nevermore3d/StealthMax/UserMods/Lid Front Hinge - Annex (by LarZem)/README.md

A Lid Front Hinge with custom engraving.
