nevermore3d/StealthMax/UserMods/Nevermore StealthMax PCB (by Isik's Tech)/README.md

[Nevermore StealthMax PCB (GitHub Repository)](https://github.com/xbst/Nevermore-PCB)
