nevermore3d/StealthMax/UserMods/Top Panel Mount (by 0ndsk4)/README.md

An early prototype top panel mount for the StealthMax which has since been discontinued in favor of the Direct On Panel Mount. 
Requires a Voron cutout in the top panel.
