nevermore3d/StealthMax/assets/_unsorted/PCO/README.md

# **Photocatalytic Addon**

Note: As of yet unknown efficiency - print for feedback or improvements (within Creative Commons Attribution) to make this addon as awesome as possible!

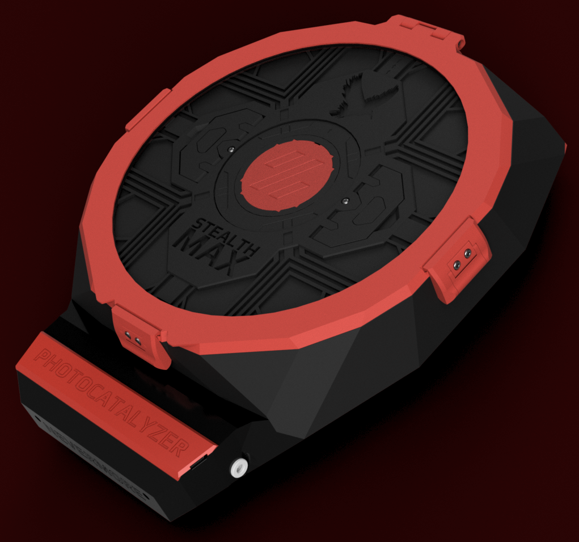
[picture p13: assets/renders/pco2.png]


# **PCO Filtration Addon: A Sun-Inspired Solution for Cleaner Air**

PCO Filtration ingeniously mirrors what the sun accomplishes with VOCs (Volatile Organic Compounds) in our atmosphere. Under natural conditions, UV rays from the sun interact with VOCs and, with the help of other elements in the air, break them down into "harmless" CO<sub>2</sub>. What if we could harness this process in our filtration systems?

**UVC** lights, set at a non-ozone-producing safe wavelength of 275nm, energize a **TiO<sub>2</sub>** (titanium dioxide) mesh, triggering electron conformation changes. Water molecules passing by react with the energized mesh, producing **hydroxyl radicals** and other reactive species that **"attack" VOCs**, effectively chopping them into smaller pieces. 

While simple VOCs can be broken down to the smallest unit of CO<sub>2</sub> rapidly, larger and more complex VOCs might necessitate multiple passes and hydroxyl radical "chops". Over time, the photocatalytic filter addon progressively degrades the contaminants. 

# Utility Across Various Fronts:
**Enhanced Efficiency:** 

VOCs that resist carbon capture may transform into a different type of VOC that is more readily trapped by filtration media, thereby enhancing the combined efficiency. Although photocatalytic filtration is generally slower than swift HEPA or carbon capture, it plays a crucial role.

**Persistent Cleanliness**: 

The PCO addon can operate even between prints to counteract styrene residue from surface off-gassing, or even from the carbon filtration media itself as the carbon ages, ensuring cleaner air for extended periods.

**Adaptability to Heat**: 

As the chamber’s temperature rises, the efficiency of carbon diminishes. Approximately at 60°C, carbon filtration becomes suboptimal. Conversely, photocatalytic reactivity benefits from the heat energy in the air, positioning the PCO addon as an excellent strategy to conserve carbon by allowing it to cool off while utilizing the heat to eliminate VOCs photocatalytically!

# BOM and Materials for an Alpha unit

Note: These are affiliate links. Please use them to support the project at no additional cost. Or don't - that's up to you!
| | Amount | Part | Source |
| ---- | ----: | ---- | :----: |
| **Electronics** |  2 pc | 14520 275nnm UVC (2.5W _or_ 6W) <sup>1</sup> | [AliExpress](https://s.click.aliexpress.com/e/_DDsC6F1) <BR>[AliExpress](https://s.click.aliexpress.com/e/_DDy4ivB)<BR>[AliExpress](https://www.aliexpress.com/item/4000898731245.html) |
| |  1 pcs | TiO<sub>2</sub> Photocatalysis Mesh <sup>2</sup> | [AliExpress](https://s.click.aliexpress.com/e/_DC8levV) |
| |  1 pcs | HEPA filter (for Xiaomi Mijia G1) | [AliExpress](https://s.click.aliexpress.com/e/_EGPsFBt) |
| |  2 pc | 3010 Blower Fans | [AliExpress](https://s.click.aliexpress.com/e/_DCLQtaj) |
| |  1 pc | 12V Single Channel Relay | [AliExpress](https://s.click.aliexpress.com/e/_Dmt3tRH) |
| **Fasteners** |  1 pcs | M8 threaded DC connector | [AliExpress](https://www.aliexpress.com/item/33001103693.html?spm=a2g0o.order_list.order_list_main.89.50ea1802RQAeZj) |
| | 8 pcs | M3x6 BHCS <sup>3</sup> | [AliExpress](https://s.click.aliexpress.com/e/_DduS2Vn) |
| | 6 pcs | M3x10 SHCS | [AliExpress](https://s.click.aliexpress.com/e/_DkxhzGZ) |
| |  4 pc | M3 Hex Nut | |
| |  2 pc | M3xD5.0xL4.0 Heat Set Inserts  | [AliExpress](https://s.click.aliexpress.com/e/_DeVF8rT) | |  

*<sup>1</sup>*  2.5W likely enough, but a stronger light will make a stronger reaction and give margin for UV degradation (80% strength left after 1000hrs seems pretty standard), but its unknown if the added heat creates a problem.<br>
*<sup>2</sup>*  3mm mesh cut with scissors to two pieces of approximately 128x40mm. A single 500x500mm sheet will thus be enough for _alot_ of TiO<sub>2</sub> filters<br>
*<sup>3</sup>*  Two of these slots are made for SHCS bolts if you've got them, but BHCS will fit just as well<br>

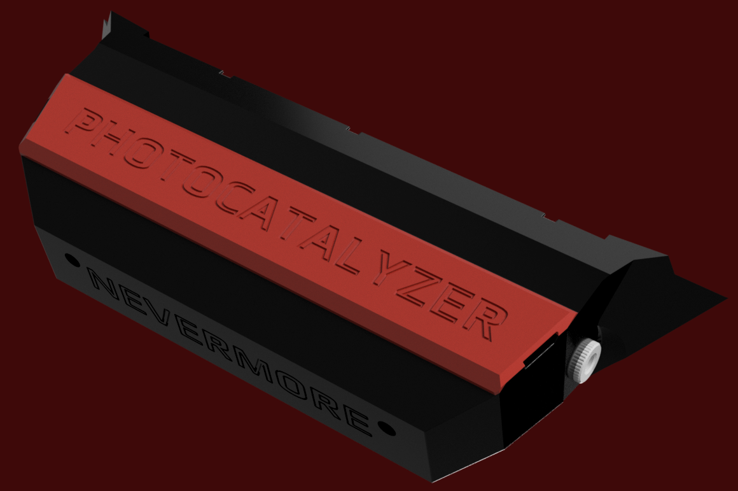
[picture p14: assets/renders/pco1.png]
