nevermore3d/StealthMax/assets/_unsorted/Stealthmax_S/README.md

StealthMax
# **Stealthmax [S]**
Lets decrease size a bit shall we, in order to print the Stealthmax on machines with a 250mm bed? 

**StealthMax [S]** is what we end up with - reworked from the ground up, its both 20% [**S**]maller than a regular Stealthmax, as well as much more [**S**]ilent due to the smaller, lower noise fan. See BOM below (purchase links linked on the main page).

- The 65mm GPU Fan has been swapped for a [**60mm Delta KFB0612HAFDB**](https://www.onetwo3d.co.uk/product/delta-kfb0612hafdb-fan/?wpam_id=2) It has less air flow at 9.15cfm unrestricted, but on the other hand is much less noisy. The unrestrictive nature of a stealthmax circular basket also allows for much more usable airflow from this fan compared to a smaller filter design. 
- The panel has shrunken to **200mm @ 3mm** thickness.
- Mounting points for VOC sensors has changed compared to the regular stealthmax.
- **Hepa filters** have been changed to new [**Nevermore Mini HEPA**](https://www.onetwo3d.co.uk/product/hepa-filter-for-nevermore-mini/?wpam_id=2), which means the total carbon depth (equaling efficiency) of the filter has not decreased more than a bit over one centimeter compared to the original Stealthmax.
- Quick and easy sourcing? Check out the electronics/fasteners/hepa/carbon [**Stealthmax S Filter Kit**](https://www.onetwo3d.co.uk/product/nevermore-stealthmax-s-filter-kit-advanced/?wpam_id=2) from OT3D!
- Most everything else remains the same from the regular BOM, including sensors, pico, buck converter, with just a few minor bolt changes: see out interactive [BOM / Sourcing Guide](https://bit.ly/NeveremoreStealthMaxBOM)

Heres how the smaller version compares to the larger:
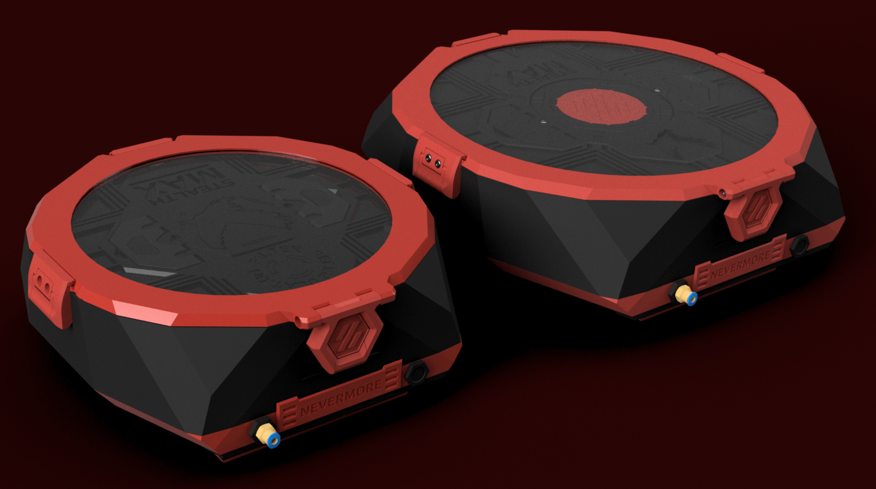
[picture p15: assets/renders/sm_250_300_comparison.png]

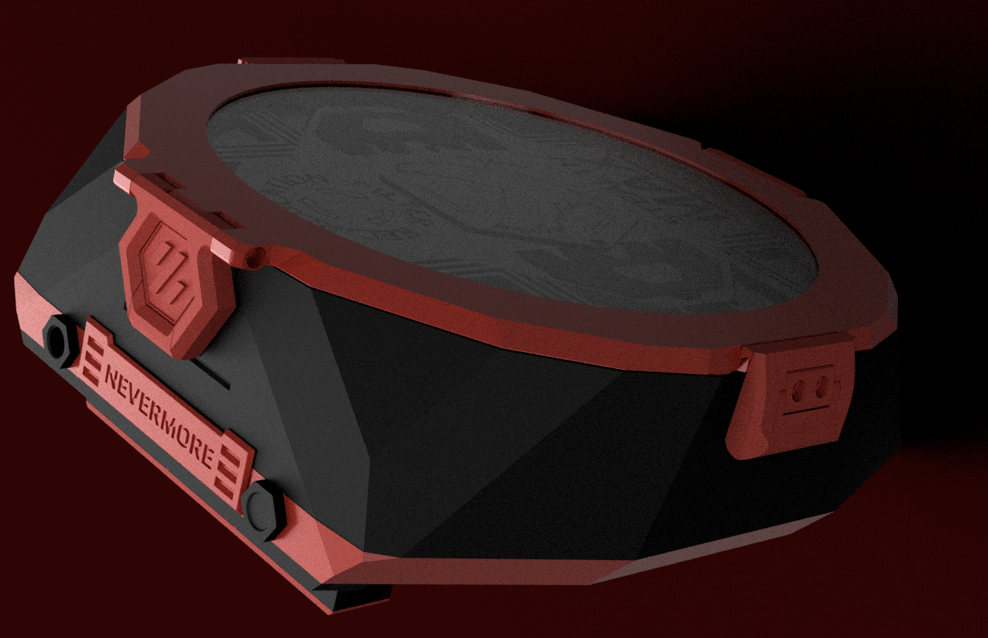
[picture p16: assets/renders/sm_250.png]
