nevermore3d/StealthMax/STLs/4_AddOns/4.1_PCOFiltration/readme.md

NOTE: The PCO Addon will be replaced with a PCO Hub module - more efficient than the original prototype - in the coming year. Stay tuned.
