nevermore3d/StealthMax/STLs/3_Lid/3.3_LidLatch.stl

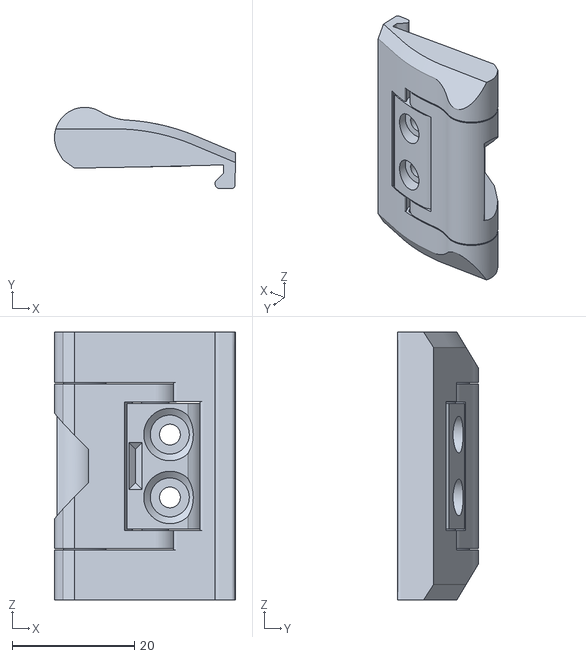
[picture p92: CAD file, 2024-05-04]
STLs/3_Lid/3.3_LidLatch.stl
29.6 x 13.3 x 43.9
