nevermore3d/StealthMax/STLs/3_Lid/StealthMax/M_3.0_LidFrame.stl

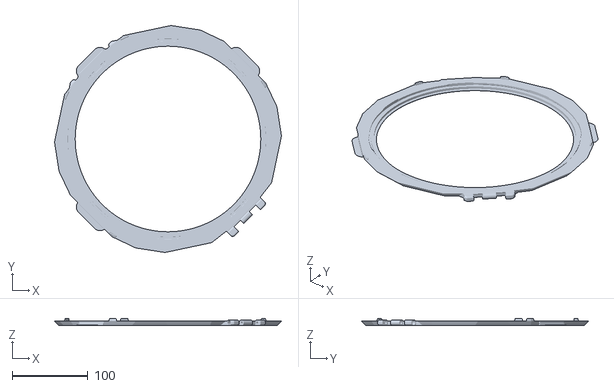
[picture p93: CAD file, 2024-05-31]
STLs/3_Lid/StealthMax/M_3.0_LidFrame.stl
300.3 x 300.3 x 9.00
