nevermore3d/StealthMax/STLs/3_Lid/StealthMax_S/S_3.0_LidFrame.stl

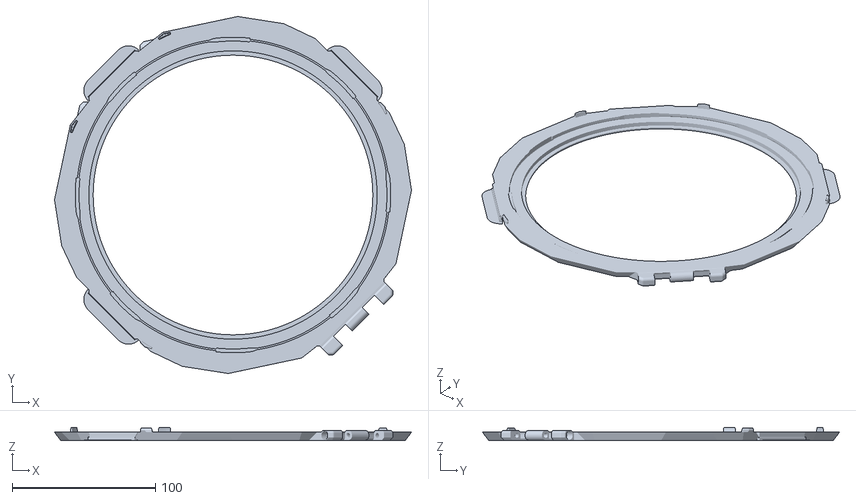
[picture p94: CAD file, 2024-05-31]
STLs/3_Lid/StealthMax_S/S_3.0_LidFrame.stl
249.3 x 249.3 x 9.00
