nevermore3d/StealthMax/STLs/4_AddOns/4.0_CPAPTubeIntake/4.0.0_IntakeAdapterLeft.stl

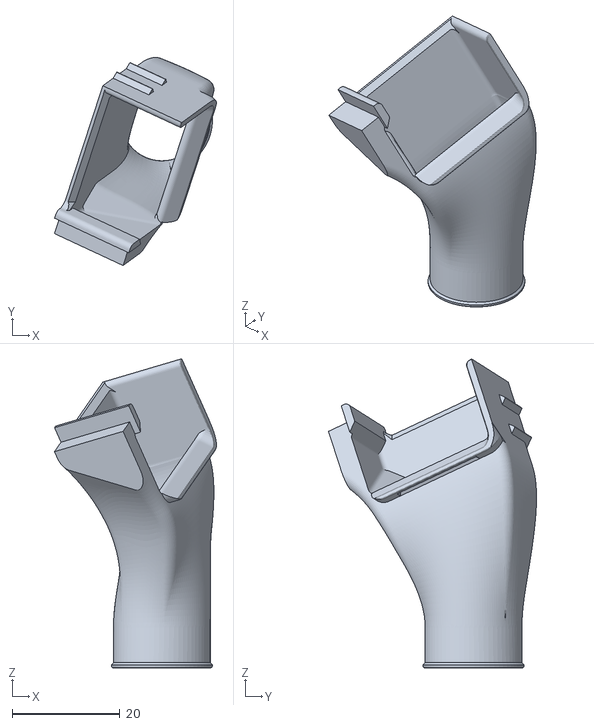
[picture p95: CAD file, 2024-08-18]
STLs/4_AddOns/4.0_CPAPTubeIntake/4.0.0_IntakeAdapterLeft.stl
30.1 x 38.7 x 57.4
