nevermore3d/StealthMax/UserMods/[Parametric] Exhaust Pipe (by FatalBulletHit)/STLs/ExhaustPipe_DOPM_4mm.stl

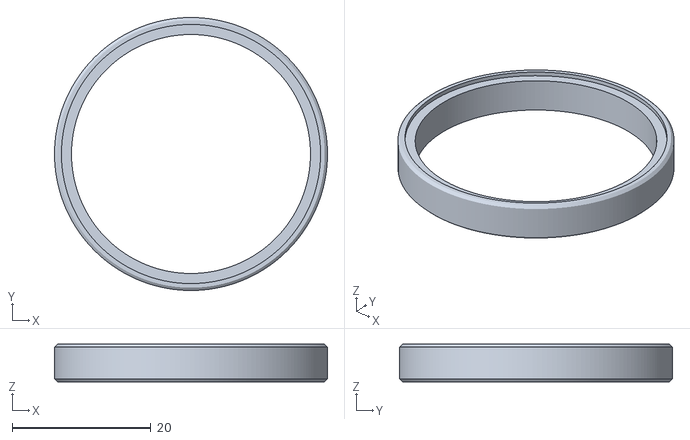
[picture p96: CAD file, 2024-03-18]
UserMods/[Parametric] Exhaust Pipe (by FatalBulletHit)/STLs/ExhaustPipe_DOPM_4mm.stl
39.3 x 39.3 x 5.40
