nevermore3d/StealthMax/UserMods/[Parametric] Lid Frame (by 0ndsk4)/4mm/S_LidPanelHolder_4mm.stl

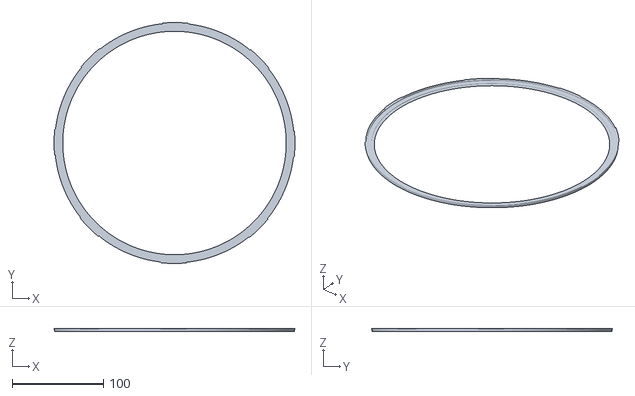
[picture p97: CAD file, 2023-06-20]
UserMods/[Parametric] Lid Frame (by 0ndsk4)/4mm/S_LidPanelHolder_4mm.stl
264.8 x 264.8 x 3.40
