nevermore3d/StealthMax/UserMods/[Parametric] Lid Frame (by 0ndsk4)/One_Eighth_in_10inch/S_LidPanelHolder_One_Eighth_in_10inch.stl

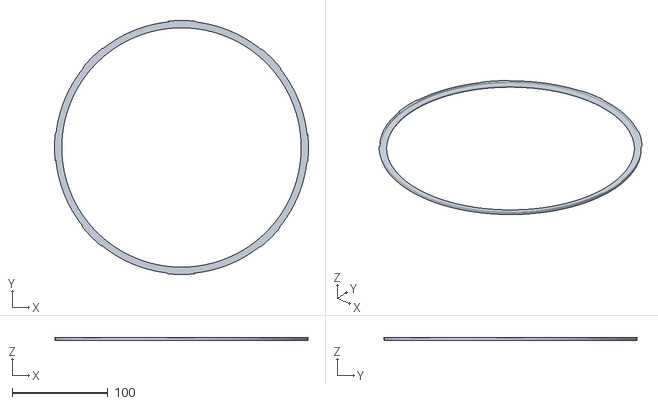
[picture p98: CAD file, 2023-06-20]
UserMods/[Parametric] Lid Frame (by 0ndsk4)/One_Eighth_in_10inch/S_LidPanelHolder_One_Eighth_in_10inch.stl
264.8 x 264.8 x 3.40
