nevermore3d/StealthMax/UserMods/Bowden Cap - ECAS (by Blamm)/BowdenCap_ECAS.stl

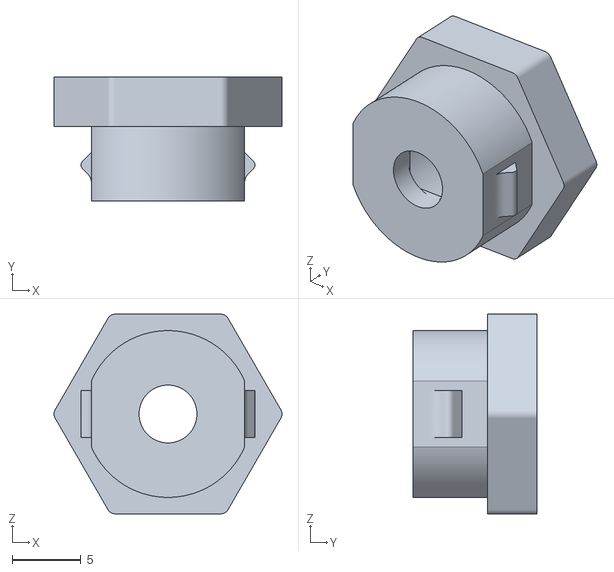
[picture p100: CAD file, 2024-10-31]
UserMods/Bowden Cap - ECAS (by Blamm)/BowdenCap_ECAS.stl
16.5 x 9.00 x 14.5
