nevermore3d/StealthMax/UserMods/Bowden Cap - PG7 (by FatalBulletHit)/Bowden Cap PG7 (by FatalBulletHit).step

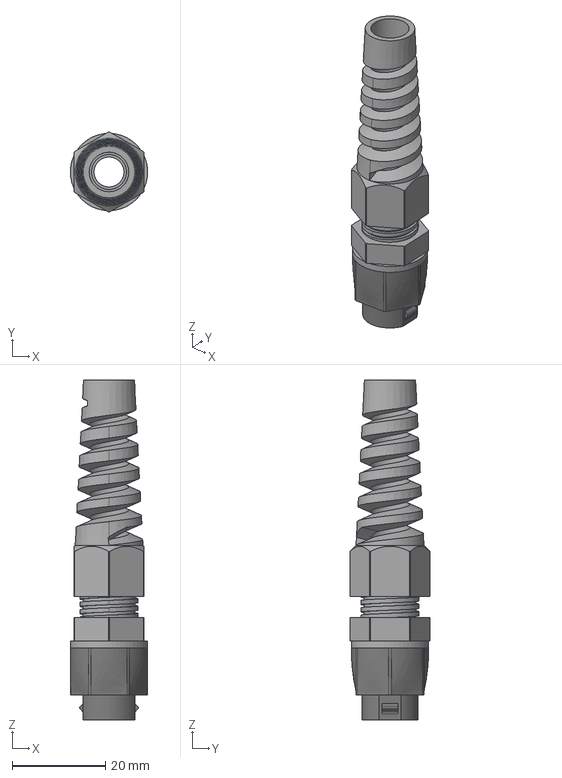
[picture p101: CAD file, 2024-05-31]
UserMods/Bowden Cap - PG7 (by FatalBulletHit)/Bowden Cap PG7 (by FatalBulletHit).step
16.6 x 17.2 x 73.0 mm
1.3b_BowdenCap_Open
bsspx-21-w_1
