nevermore3d/StealthMax/UserMods/Cable Entry Cap - Micro-Fit 5 Pin (by everydaybludger)/CableEntryCap_MicroFit5.stl

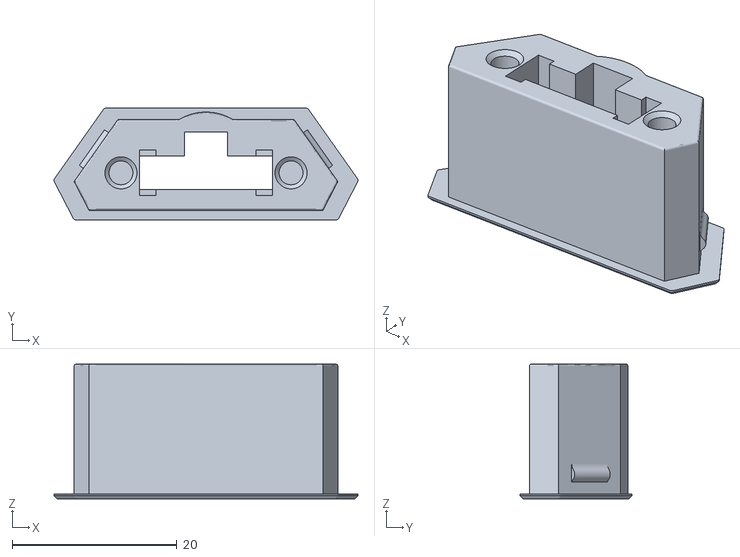
[picture p102: CAD file, 2024-03-18]
UserMods/Cable Entry Cap - Micro-Fit 5 Pin (by everydaybludger)/CableEntryCap_MicroFit5.stl
36.9 x 13.6 x 16.4
