nevermore3d/StealthMax/UserMods/Cable Entry Cap - Open Inlet (by AdamV3D)/Cable Entry Cap - Open Inlet (by AdamV3D).step

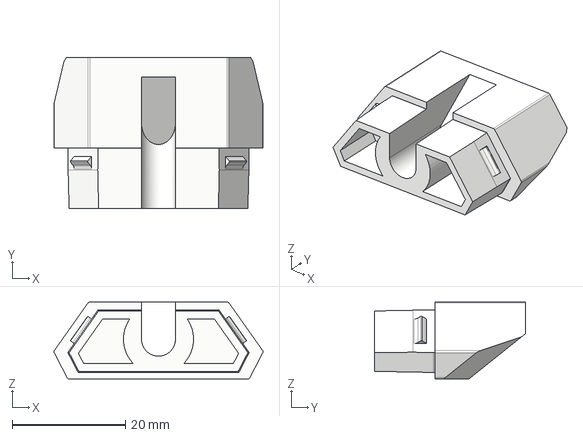
[picture p103: CAD file, 2024-05-31]
UserMods/Cable Entry Cap - Open Inlet (by AdamV3D)/Cable Entry Cap - Open Inlet (by AdamV3D).step
36.9 x 26.7 x 13.6 mm
