nevermore3d/StealthMax/UserMods/Cable Entry Cap - QtPy (by fboc)/CableEntryCap_QtPy.stl

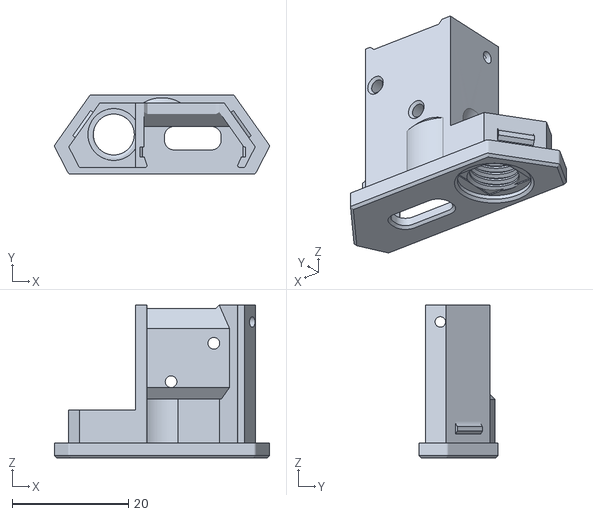
[picture p104: CAD file, 2023-12-06]
UserMods/Cable Entry Cap - QtPy (by fboc)/CableEntryCap_QtPy.stl
36.9 x 13.6 x 26.3
