nevermore3d/StealthMax/UserMods/Cable Entry Cap - USB (by Tuba)/CableEntryCap_USB.stl

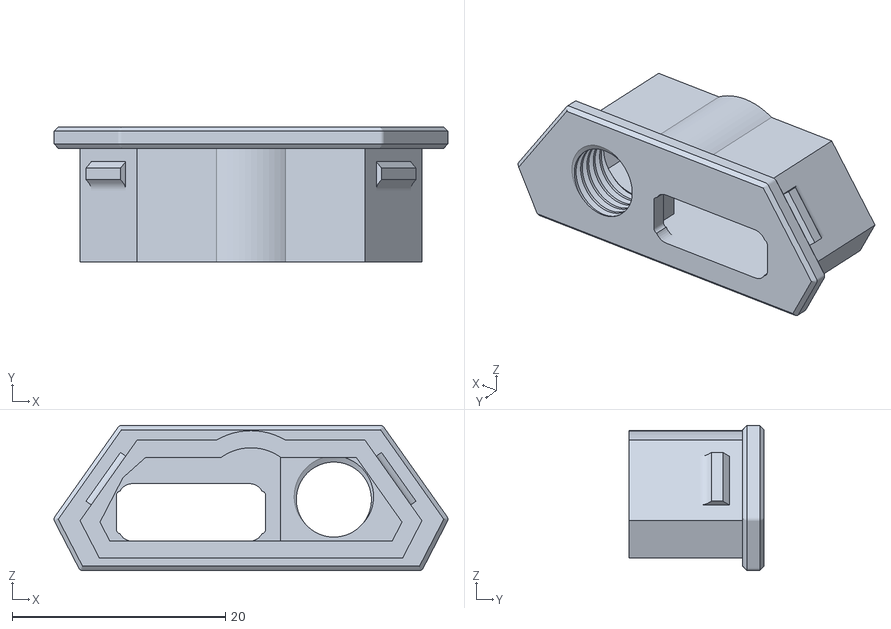
[picture p105: CAD file, 2023-10-12]
UserMods/Cable Entry Cap - USB (by Tuba)/CableEntryCap_USB.stl
36.9 x 12.7 x 13.6
