nevermore3d/StealthMax/UserMods/Chamber Exhaust Connection - Upwards Flow (by AdamV3D)/Chamber Exhaust Connection - Upwards Flow (by AdamV3D).step

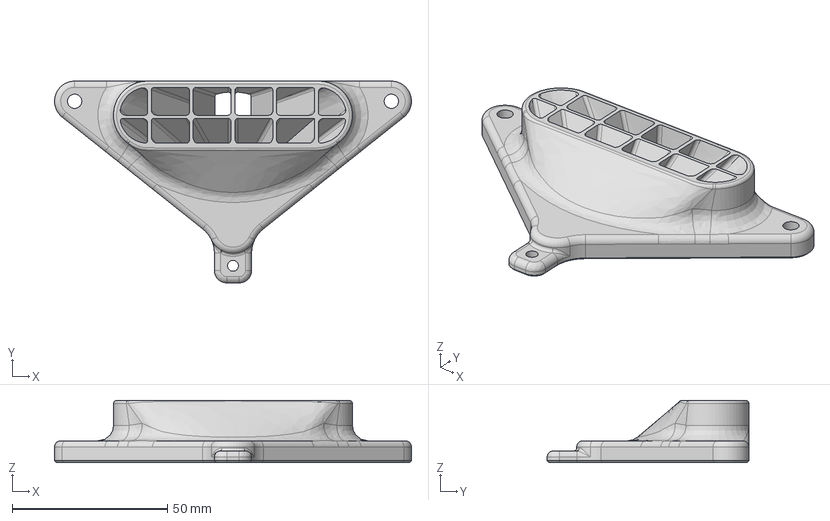
[picture p106: CAD file, 2024-05-31]
UserMods/Chamber Exhaust Connection - Upwards Flow (by AdamV3D)/Chamber Exhaust Connection - Upwards Flow (by AdamV3D).step
115.0 x 65.0 x 20.0 mm
