nevermore3d/StealthMax/UserMods/ERCF Mount (by BO_Andy)/ERCFMount.stl

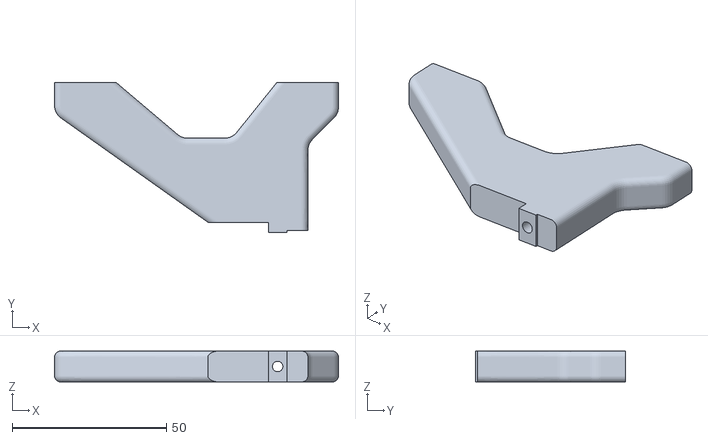
[picture p107: CAD file, 2023-12-10]
UserMods/ERCF Mount (by BO_Andy)/ERCFMount.stl
92.0 x 48.6 x 10.0
