nevermore3d/StealthMax/UserMods/Fan Wire Pin (Extra Long) (by SirRenix)/FanWirePin_ExtraLong.stl

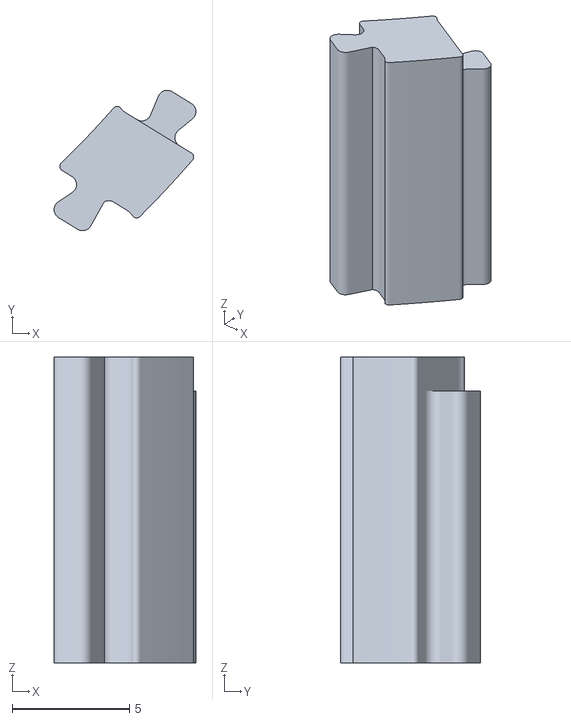
[picture p108: CAD file, 2024-03-13]
UserMods/Fan Wire Pin (Extra Long) (by SirRenix)/FanWirePin_ExtraLong.stl
6.05 x 5.99 x 13.1
