nevermore3d/StealthMax/UserMods/Flow Chamber Fan Hole Plug (by SirRenix)/FlowChamberFanHolePlug.stl

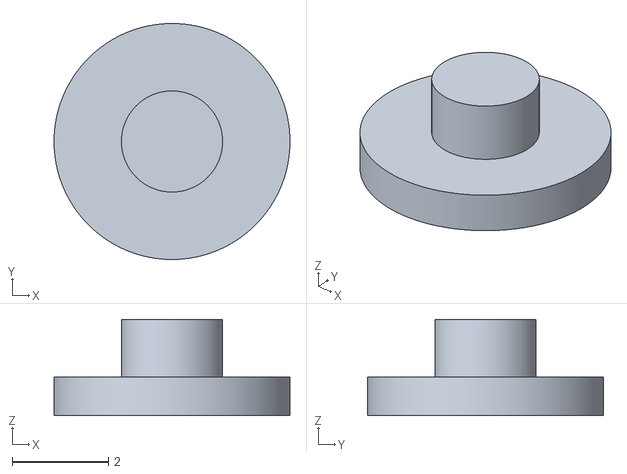
[picture p109: CAD file, 2024-03-18]
UserMods/Flow Chamber Fan Hole Plug (by SirRenix)/FlowChamberFanHolePlug.stl
4.90 x 4.90 x 2.00
