nevermore3d/StealthMax/UserMods/Ghetto Panel (by TessaKavanagh)/M_GhettoPanel.stl

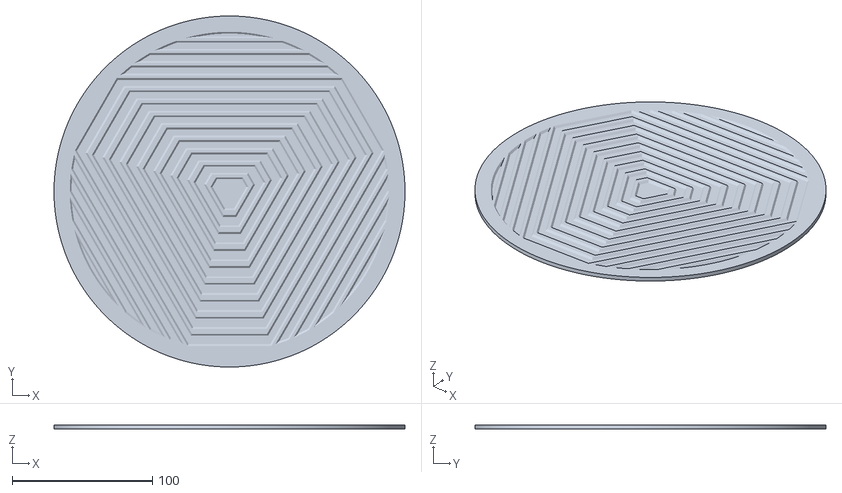
[picture p110: CAD file, 2024-03-13]
UserMods/Ghetto Panel (by TessaKavanagh)/M_GhettoPanel.stl
250.0 x 250.0 x 3.00
