nevermore3d/StealthMax/UserMods/Lid Frame - Extra Clearance (by AdamV3D)/Lid Frame - Extra Clearance (by AdamV3D).step

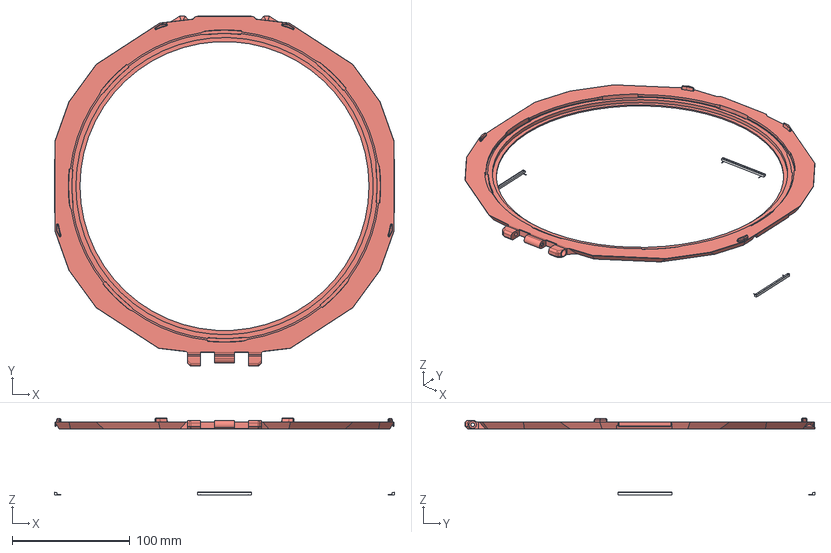
[picture p111: CAD file, 2024-05-31]
UserMods/Lid Frame - Extra Clearance (by AdamV3D)/Lid Frame - Extra Clearance (by AdamV3D).step
288.8 x 297.2 x 65.0 mm
