nevermore3d/StealthMax/UserMods/Lid Front Hinge - 2 Part Version (by AdamV3D)/Lid Front Hinge - 2 Part Version (by AdamV3D).step

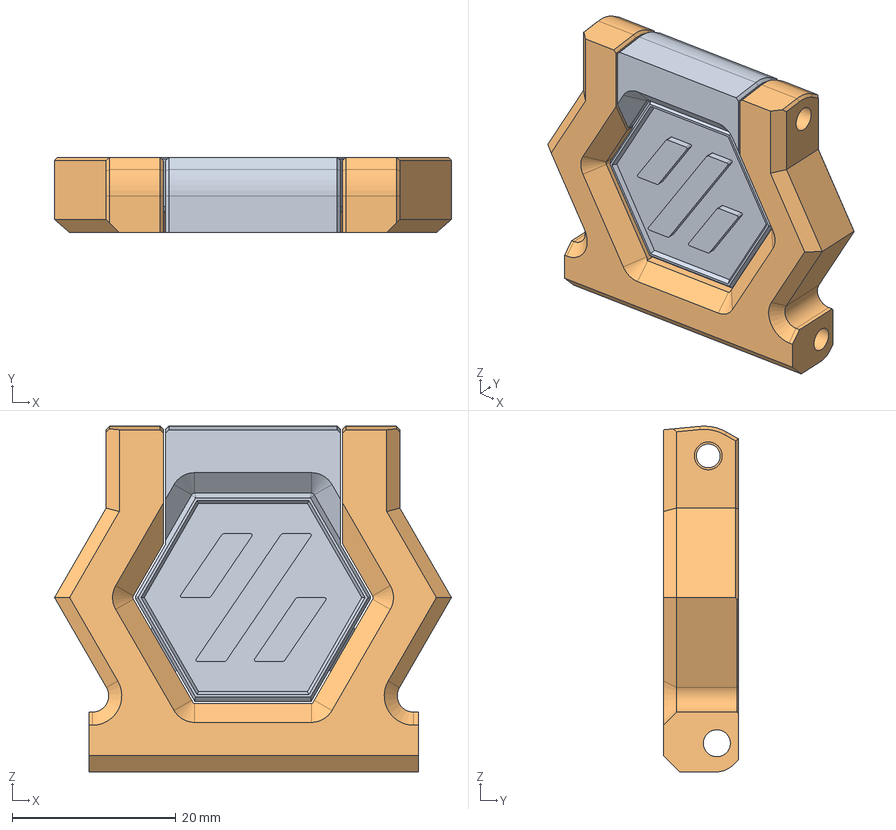
[picture p112: CAD file, 2024-05-31]
UserMods/Lid Front Hinge - 2 Part Version (by AdamV3D)/Lid Front Hinge - 2 Part Version (by AdamV3D).step
48.5 x 9.18 x 42.2 mm
