nevermore3d/StealthMax/UserMods/Lid Front Hinge - Annex (by LarZem)/LidFrontHinge_Annex.stl

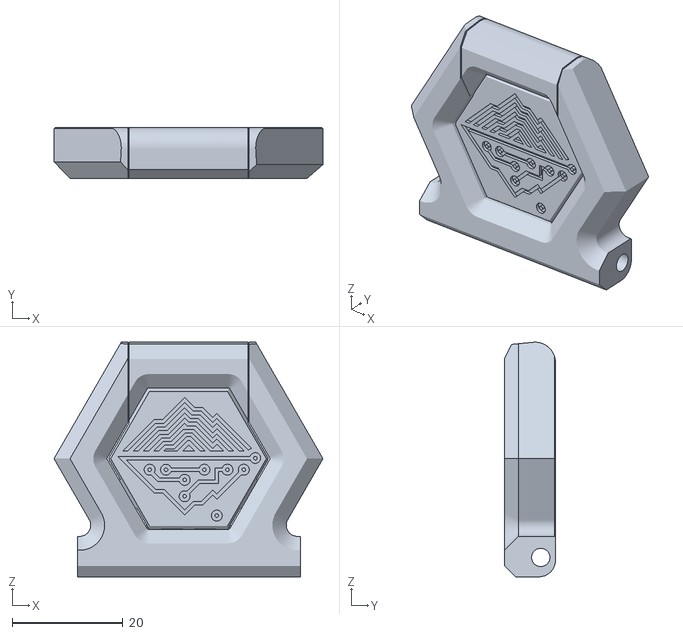
[picture p113: CAD file, 2023-12-06]
UserMods/Lid Front Hinge - Annex (by LarZem)/LidFrontHinge_Annex.stl
48.5 x 9.18 x 42.3
