nevermore3d/StealthMax/UserMods/Lid Panel Holder - Easy Turn (by AdamV3D)/Lid Panel Holder - Easy Turn (by AdamV3D).step

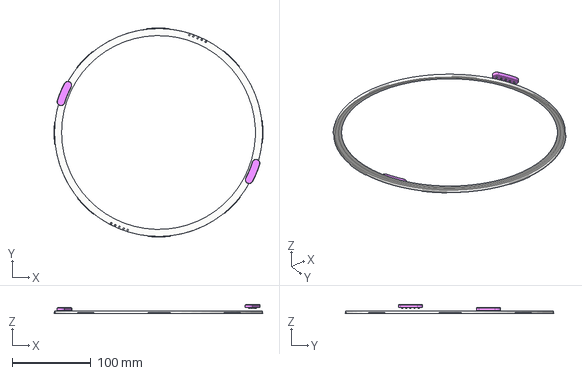
[picture p114: CAD file, 2024-05-31]
UserMods/Lid Panel Holder - Easy Turn (by AdamV3D)/Lid Panel Holder - Easy Turn (by AdamV3D).step
264.7 x 264.7 x 11.4 mm
Gripper x 2
