nevermore3d/StealthMax/UserMods/Sensor Holder - Mag Carrier (by 0ndsk4)/Sensor Holder Mag Carrier (by 0ndsk4).step

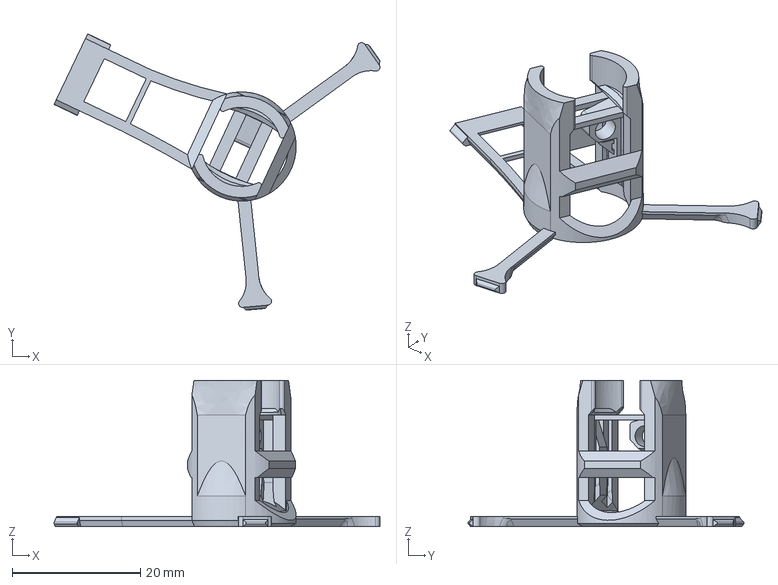
[picture p115: CAD file, 2024-03-18]
UserMods/Sensor Holder - Mag Carrier (by 0ndsk4)/Sensor Holder Mag Carrier (by 0ndsk4).step
50.8 x 43.0 x 22.8 mm
