nevermore3d/StealthMax/UserMods/Toggleable Channel DOPM FlowChamber (by VIN-y)/10_NM_StealthMax_Mod_v3-Output_Funnel.stl

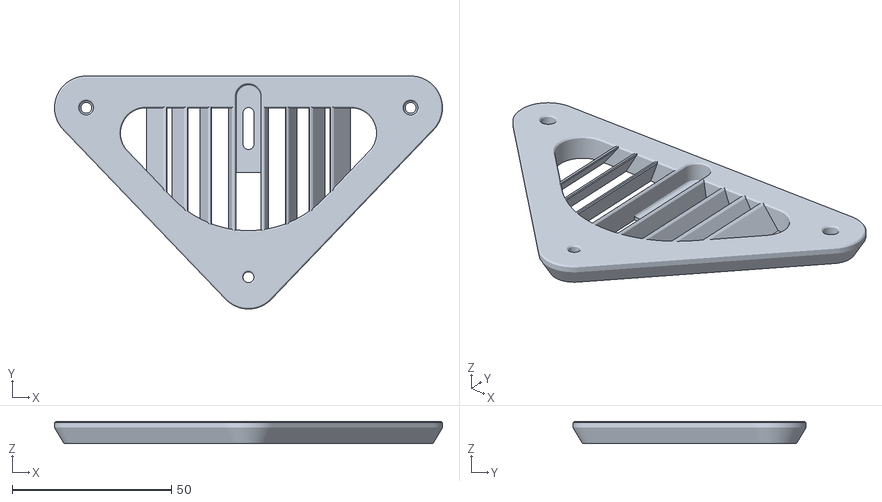
[picture p116: CAD file, 2024-10-18]
UserMods/Toggleable Channel DOPM FlowChamber (by VIN-y)/10_NM_StealthMax_Mod_v3-Output_Funnel.stl
121.9 x 73.2 x 7.00
