nevermore3d/StealthMax/UserMods/Toggleable Channel DOPM FlowChamber (by VIN-y)/CADs/10_NM_StealthMax_Mod-Switch.step

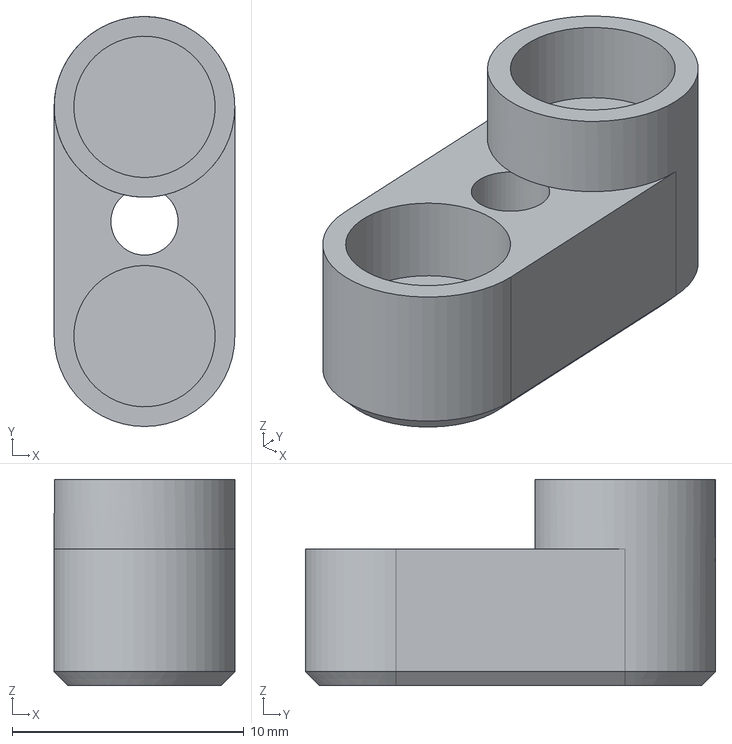
[picture p117: CAD file, 2024-10-18]
UserMods/Toggleable Channel DOPM FlowChamber (by VIN-y)/CADs/10_NM_StealthMax_Mod-Switch.step
7.80 x 17.7 x 8.90 mm
