nevermore3d/StealthMax/UserMods/Top Panel Mount (by 0ndsk4)/Top Panel Mount (by 0ndsk4).step

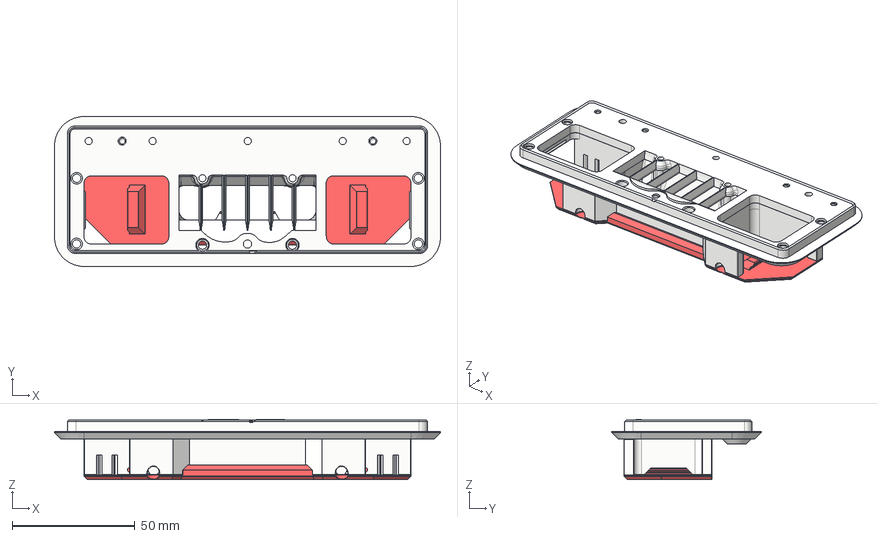
[picture p118: CAD file, 2024-03-13]
UserMods/Top Panel Mount (by 0ndsk4)/Top Panel Mount (by 0ndsk4).step
157.0 x 61.0 x 24.6 mm
Chamber Side (1)
Voron Exhaust Fitting (1)
