nevermore3d/StealthMax/UserMods/Umbilical entry via flow chamber (by igiannakas)/StealthMax 300 flow chamber for umbilical.stl

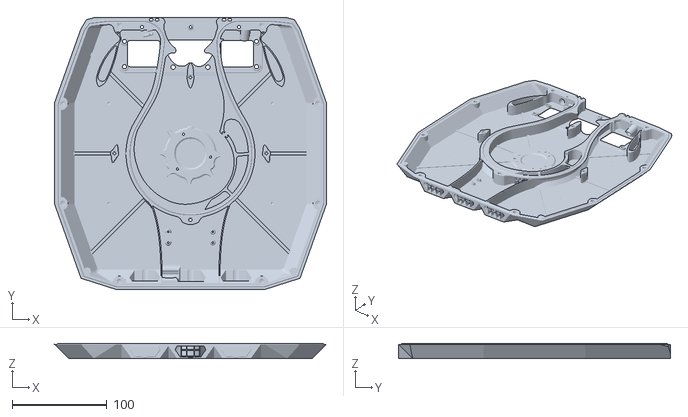
[picture p119: CAD file, 2024-05-31]
UserMods/Umbilical entry via flow chamber (by igiannakas)/StealthMax 300 flow chamber for umbilical.stl
286.4 x 286.4 x 15.9
