nevermore3d/StealthMax/UserMods/Umbilical Mount BPM (by fronti)/umbilical-mount-bpm.stl

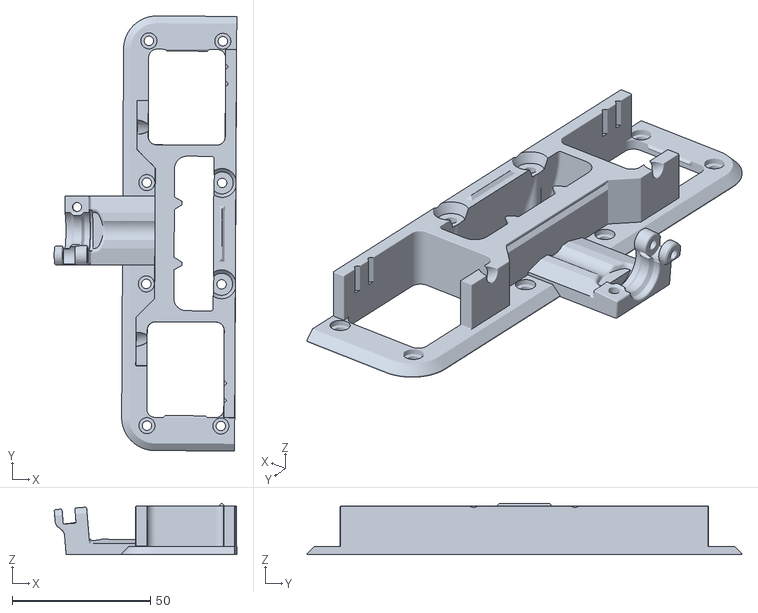
[picture p120: CAD file, 2024-12-13]
UserMods/Umbilical Mount BPM (by fronti)/umbilical-mount-bpm.stl
66.0 x 157.1 x 18.5
