nevermore3d/StealthMax/UserMods/Voron Exhaust Fitting - ERCF Filament Motion Sensor (by ManuC)/StealthMax_-_FilamentSensor-_Left.stl

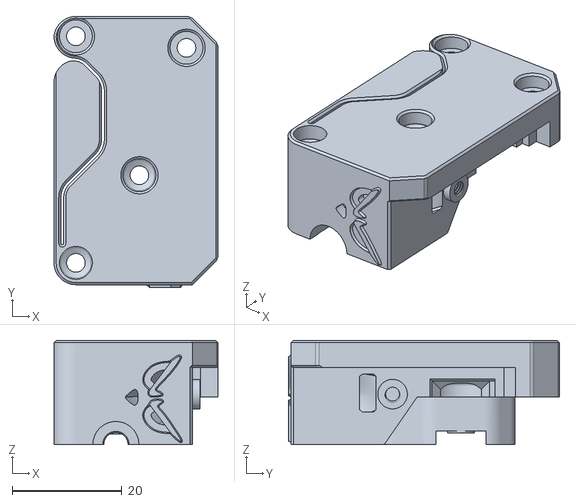
[picture p121: CAD file, 2024-03-18]
UserMods/Voron Exhaust Fitting - ERCF Filament Motion Sensor (by ManuC)/StealthMax_-_FilamentSensor-_Left.stl
29.9 x 49.5 x 19.0
