nevermore3d/StealthMax/UserMods/Voronexhaustfitting_BPM- BTT smart filament sensor/bowdencap_ptfe.stl

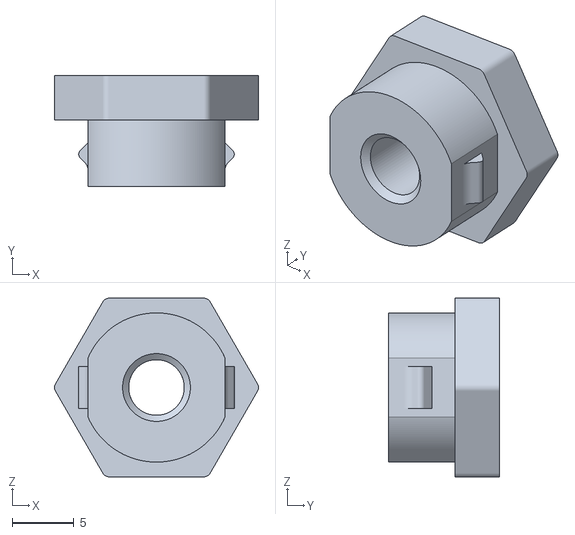
[picture p122: CAD file, 2025-01-29]
UserMods/Voronexhaustfitting_BPM- BTT smart filament sensor/bowdencap_ptfe.stl
16.5 x 9.00 x 14.5
