nevermore3d/StealthMax/STLs/0_Mount/0a_BackPanelMount/0a.2_BackPanelMountCover_BPM.stl

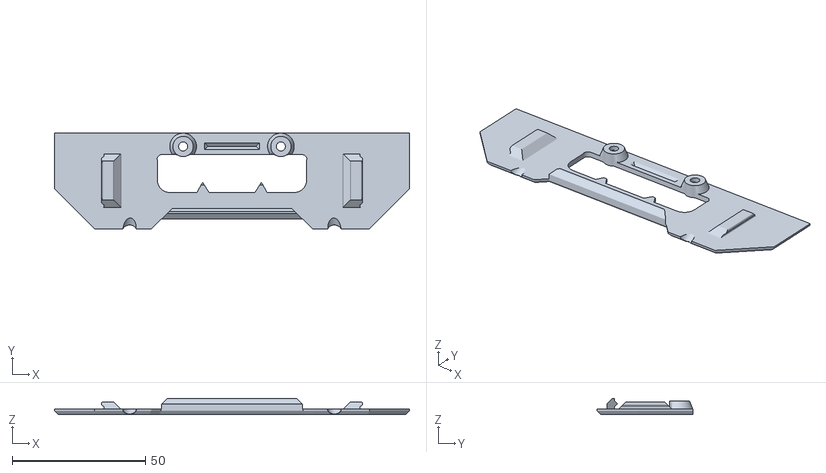
[picture p123: CAD file, 2024-03-18]
STLs/0_Mount/0a_BackPanelMount/0a.2_BackPanelMountCover_BPM.stl
133.0 x 35.9 x 6.00
