nevermore3d/StealthMax/STLs/1_FlowChamber/1.4a_CableEntryCap_M8Barrel.stl

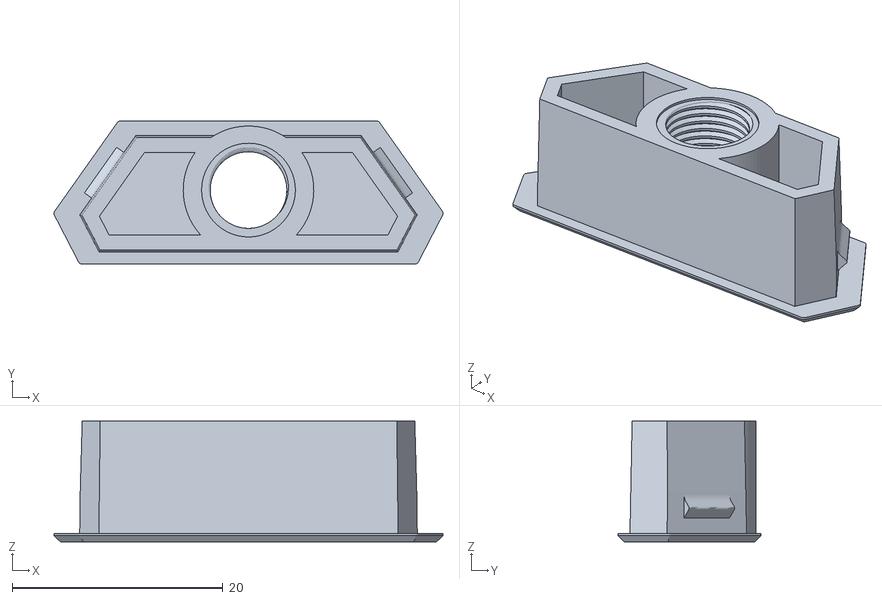
[picture p124: CAD file, 2024-03-13]
STLs/1_FlowChamber/1.4a_CableEntryCap_M8Barrel.stl
36.9 x 13.6 x 11.5
