nevermore3d/StealthMax/STLs/1_FlowChamber/1b_DirectOnPanelMount/StealthMax_S/S_1b.1_RemovableAirDuct_DOPM.stl

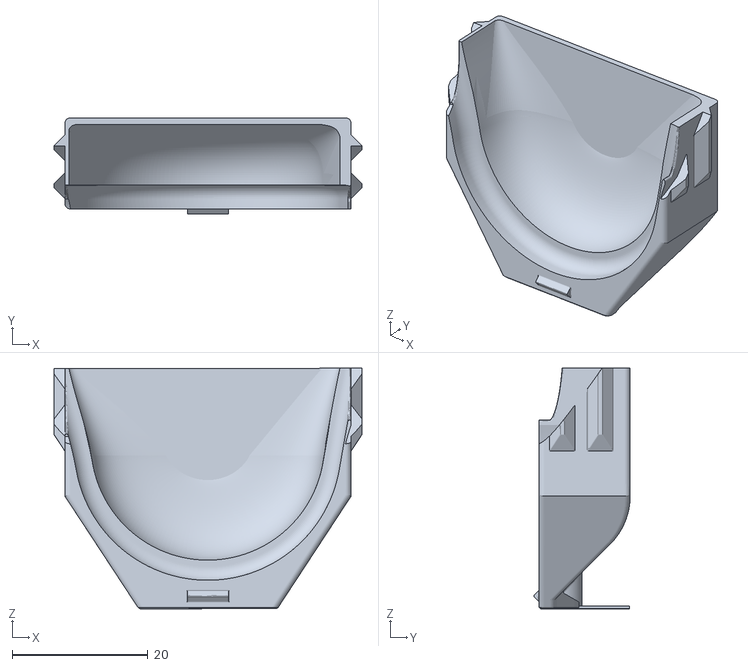
[picture p125: CAD file, 2024-03-18]
STLs/1_FlowChamber/1b_DirectOnPanelMount/StealthMax_S/S_1b.1_RemovableAirDuct_DOPM.stl
45.3 x 14.2 x 35.4
