nevermore3d/StealthMax/STLs/2_MainChamber/StealthMax/M_2.5a_LogoCap.stl

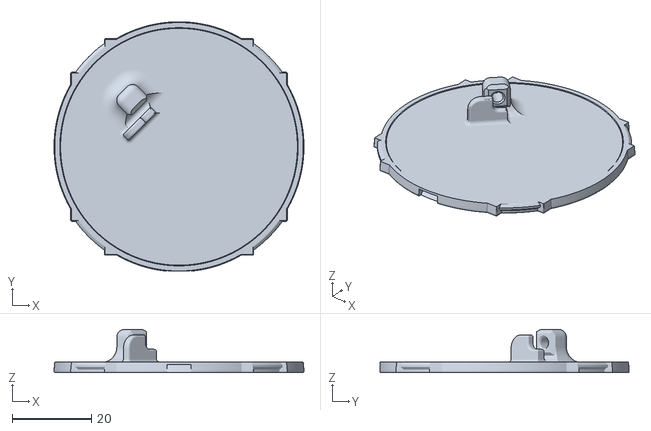
[picture p126: CAD file, 2024-05-31]
STLs/2_MainChamber/StealthMax/M_2.5a_LogoCap.stl
63.1 x 63.0 x 10.9
