nevermore3d/StealthMax/STLs/2_MainChamber/StealthMax_S/S_2.5_SensorHolder.stl

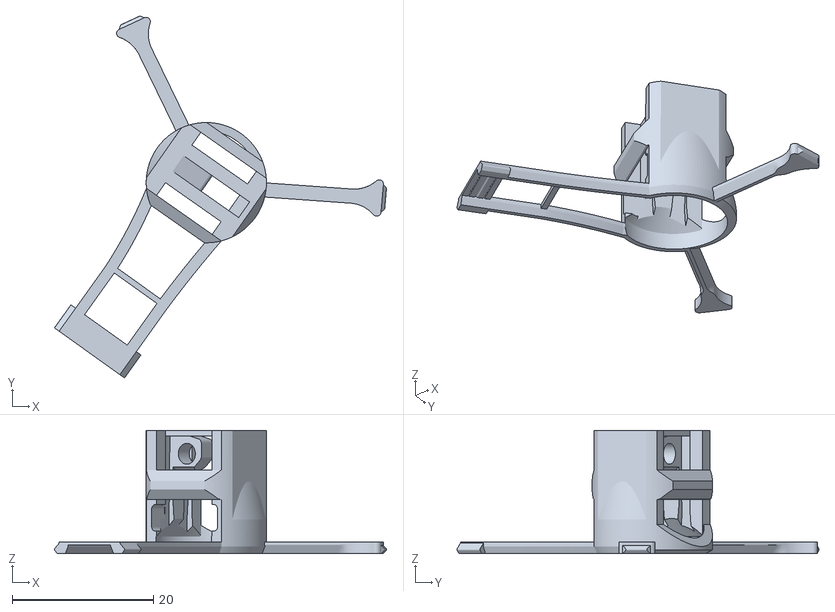
[picture p127: CAD file, 2024-03-18]
STLs/2_MainChamber/StealthMax_S/S_2.5_SensorHolder.stl
46.9 x 51.2 x 17.4
