nevermore3d/StealthMax/STLs/3_Lid/3.2_LidFrontHinge.stl

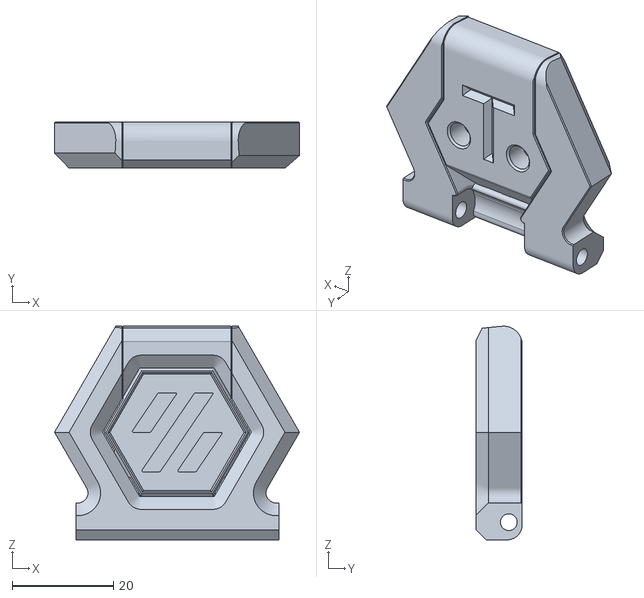
[picture p128: CAD file, 2024-03-13]
STLs/3_Lid/3.2_LidFrontHinge.stl
48.5 x 9.18 x 42.3
