nevermore3d/StealthMax/STLs/3_Lid/StealthMax_S/S_3.1_LidPanelHolder.stl

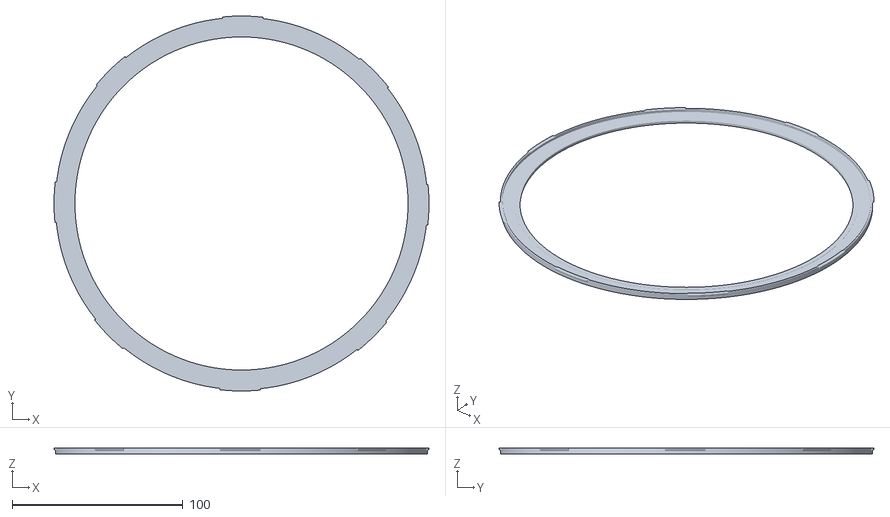
[picture p129: CAD file, 2024-03-18]
STLs/3_Lid/StealthMax_S/S_3.1_LidPanelHolder.stl
219.8 x 219.8 x 3.40
