nevermore3d/StealthMax/STLs/4_AddOns/4.0_CPAPTubeIntake/4.0.4_2020IntakeRail.stl

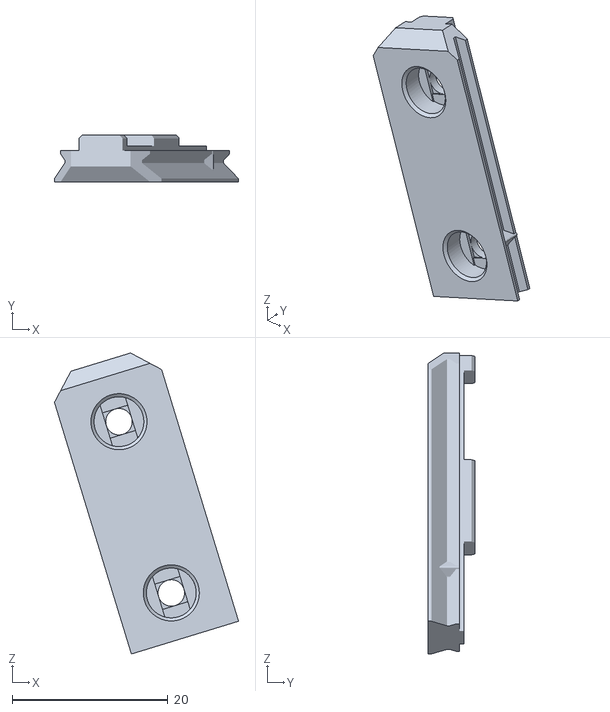
[picture p130: CAD file, 2024-08-18]
STLs/4_AddOns/4.0_CPAPTubeIntake/4.0.4_2020IntakeRail.stl
23.7 x 6.00 x 38.7
