nevermore3d/StealthMax/STLs/4_AddOns/4.1_PCOFiltration/4.1.2_PCOAdpater.stl

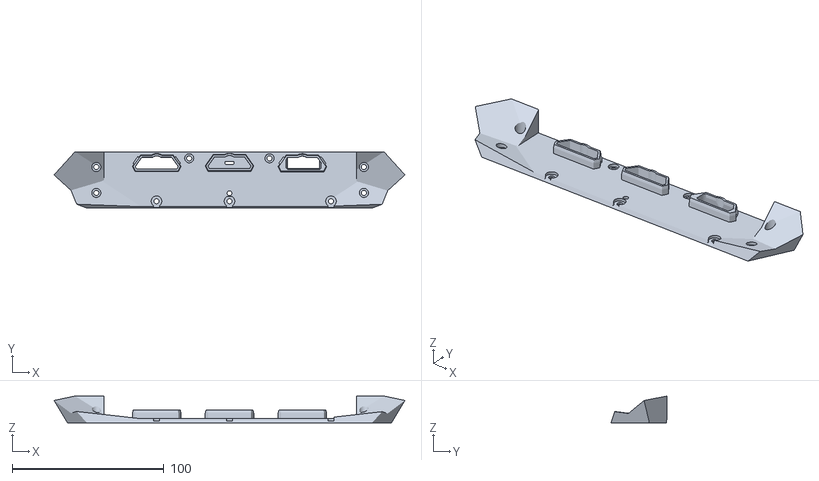
[picture p131: CAD file, 2024-03-13]
STLs/4_AddOns/4.1_PCOFiltration/4.1.2_PCOAdpater.stl
231.3 x 37.1 x 17.7
