nevermore3d/StealthMax/UserMods/[Parametric] Exhaust Pipe (by FatalBulletHit)/STLs/ExhaustPipe_DOPM_6mm.stl

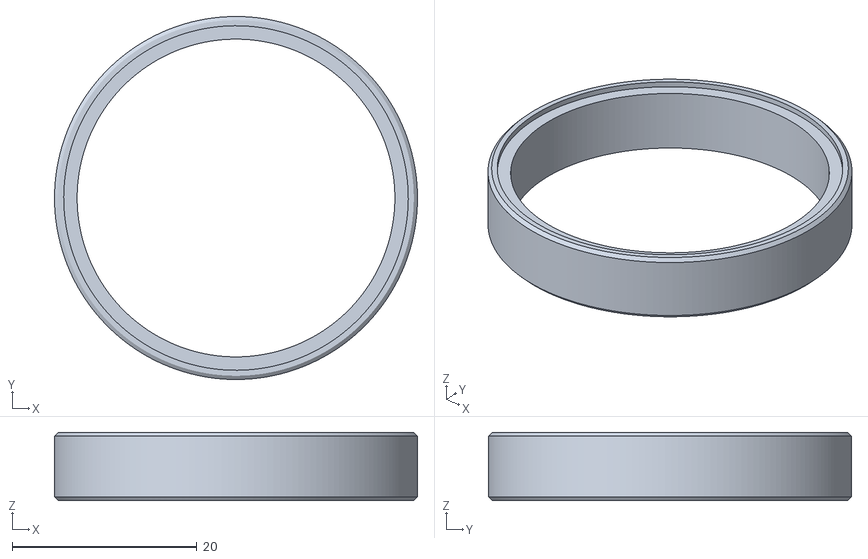
[picture p132: CAD file, 2024-03-18]
UserMods/[Parametric] Exhaust Pipe (by FatalBulletHit)/STLs/ExhaustPipe_DOPM_6mm.stl
39.3 x 39.3 x 7.40
