nevermore3d/StealthMax/UserMods/[Parametric] Lid Frame (by 0ndsk4)/4mm/S_LidFrame_4mm.stl

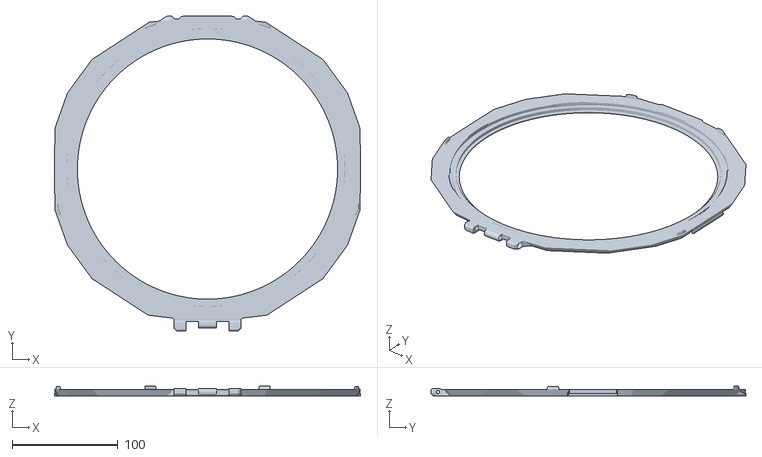
[picture p133: CAD file, 2023-06-20]
UserMods/[Parametric] Lid Frame (by 0ndsk4)/4mm/S_LidFrame_4mm.stl
288.8 x 297.2 x 9.00
