nevermore3d/StealthMax/UserMods/[Parametric] Lid Frame (by 0ndsk4)/One_Eighth_in_10inch/S_LidFrame_One_Eighth_in_10inch.stl

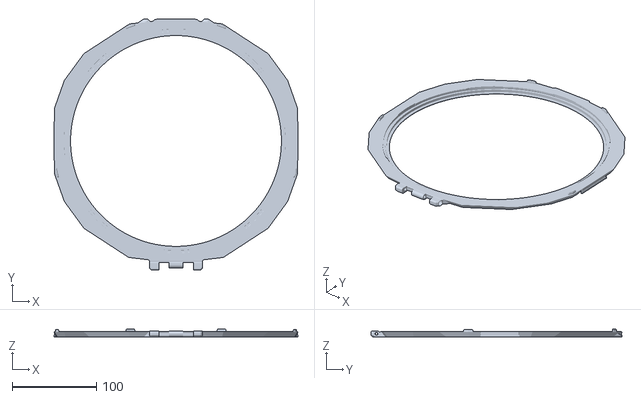
[picture p134: CAD file, 2023-06-20]
UserMods/[Parametric] Lid Frame (by 0ndsk4)/One_Eighth_in_10inch/S_LidFrame_One_Eighth_in_10inch.stl
288.8 x 297.2 x 9.00
