nevermore3d/StealthMax/UserMods/Bowden Cap - PG7 (by FatalBulletHit)/BowdenCap_PG7.stl

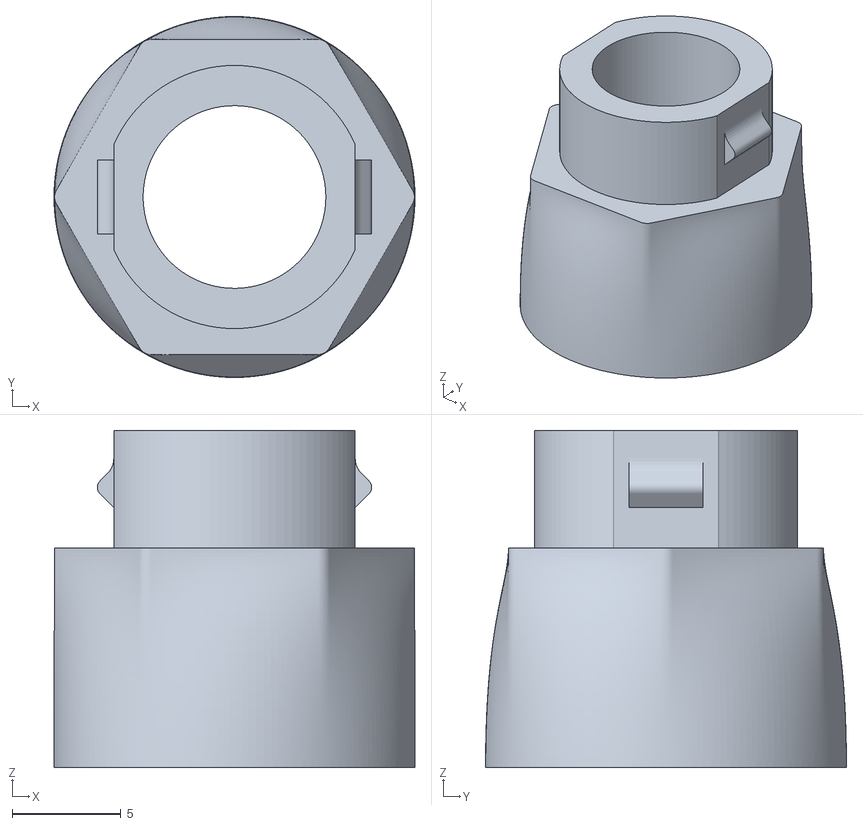
[picture p136: CAD file, 2024-05-31]
UserMods/Bowden Cap - PG7 (by FatalBulletHit)/BowdenCap_PG7.stl
16.6 x 16.6 x 15.5
