nevermore3d/StealthMax/UserMods/Cable Entry Cap - QtPy (by fboc)/Cable Entry Cap QtPy (by fboc).step

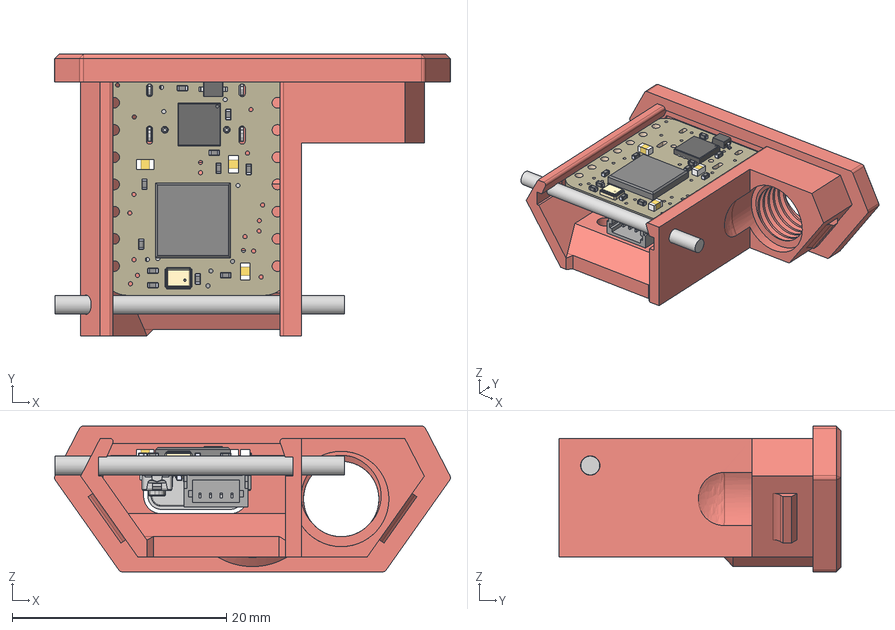
[picture p137: CAD file, 2023-12-06]
UserMods/Cable Entry Cap - QtPy (by fboc)/Cable Entry Cap QtPy (by fboc).step
36.9 x 26.3 x 13.6 mm
Cable Entry QtPy holder
Board
0805-NO x 2
JST_SH4_SKINNY
SOT23-5
SK6805_1515
SOD-323_MINI x 2
USON8_4X4
_0402NO x 17
0603-NO x 3
USB_C_CUSB31-CFM2AX-01-X
QFN56_7MM_REDUCEDEPAD
BTN_KMR2_4.6X2.8 x 2
CRYSTAL_2.5X2
filament
