nevermore3d/StealthMax/UserMods/Ghetto Panel (by TessaKavanagh)/Ghetto Panel (by TessaKavanagh).step

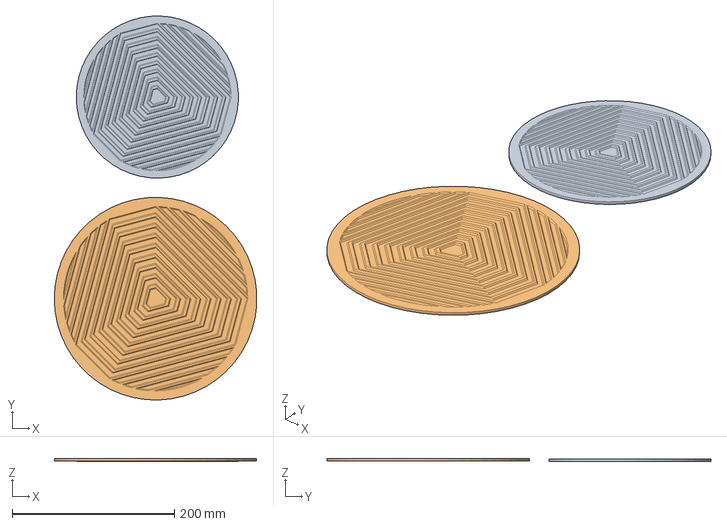
[picture p138: CAD file, 2024-03-13]
UserMods/Ghetto Panel (by TessaKavanagh)/Ghetto Panel (by TessaKavanagh).step
249.8 x 473.6 x 3.30 mm
GhettoPanel_SM_S_250
GhettoPanel_SM_300
