nevermore3d/StealthMax/UserMods/Toggleable Channel DOPM FlowChamber (by VIN-y)/10_NM_StealthMax_Mod_v3-Swich_Leave.stl

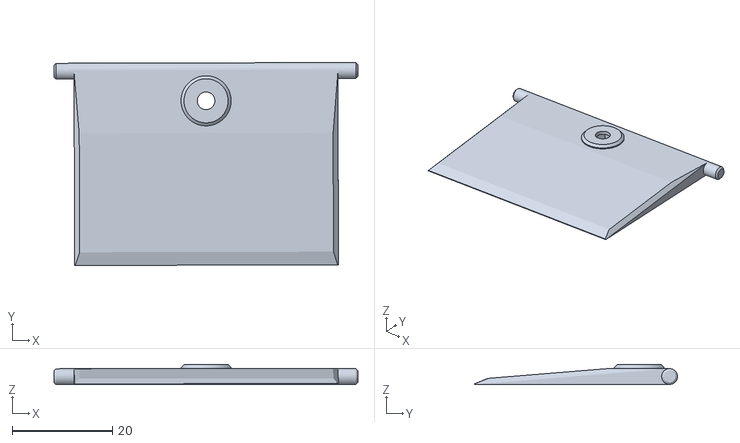
[picture p139: CAD file, 2024-10-18]
UserMods/Toggleable Channel DOPM FlowChamber (by VIN-y)/10_NM_StealthMax_Mod_v3-Swich_Leave.stl
60.7 x 40.5 x 4.02
