nevermore3d/StealthMax/UserMods/Toggleable Channel DOPM FlowChamber (by VIN-y)/CADs/10_NM_StealthMax_Mod-Intake_Funnel_x4.step

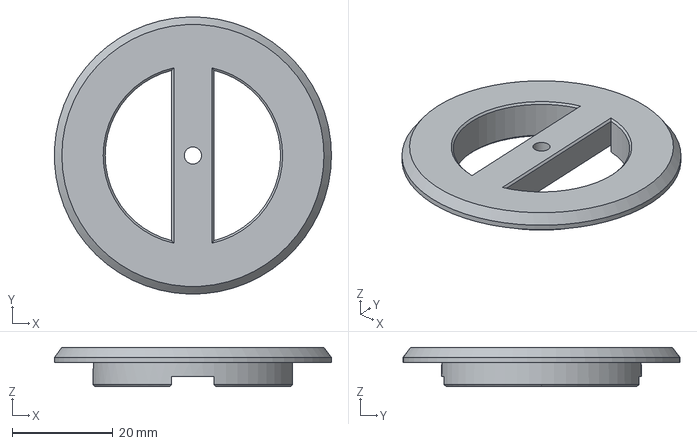
[picture p140: CAD file, 2024-10-18]
UserMods/Toggleable Channel DOPM FlowChamber (by VIN-y)/CADs/10_NM_StealthMax_Mod-Intake_Funnel_x4.step
55.0 x 55.0 x 7.80 mm
