nevermore3d/StealthMax/UserMods/Top Panel Mount (by 0ndsk4)/M_VoronExhaustFitting_TPM.stl

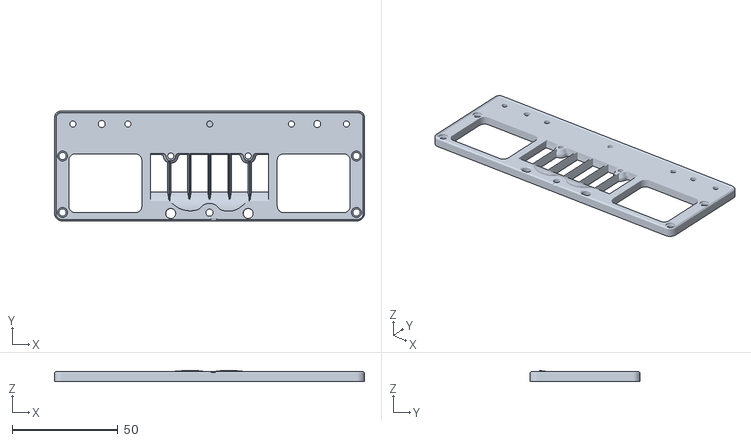
[picture p141: CAD file, 2024-03-07]
UserMods/Top Panel Mount (by 0ndsk4)/M_VoronExhaustFitting_TPM.stl
146.6 x 51.9 x 5.00
