nevermore3d/StealthMax/UserMods/Voron Exhaust Fitting - ERCF Filament Motion Sensor (by ManuC)/StealthMax_-_FilamentSensor_-_Right.stl

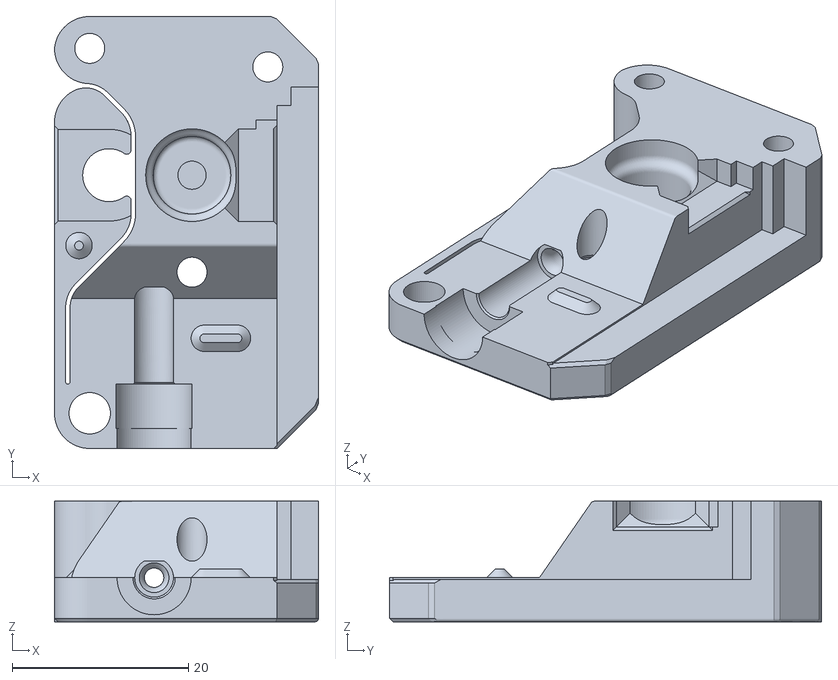
[picture p142: CAD file, 2024-03-18]
UserMods/Voron Exhaust Fitting - ERCF Filament Motion Sensor (by ManuC)/StealthMax_-_FilamentSensor_-_Right.stl
29.9 x 49.0 x 13.7
