nevermore3d/StealthMax/STLs/1_FlowChamber/1.5_FanWirePin_Spare.stl

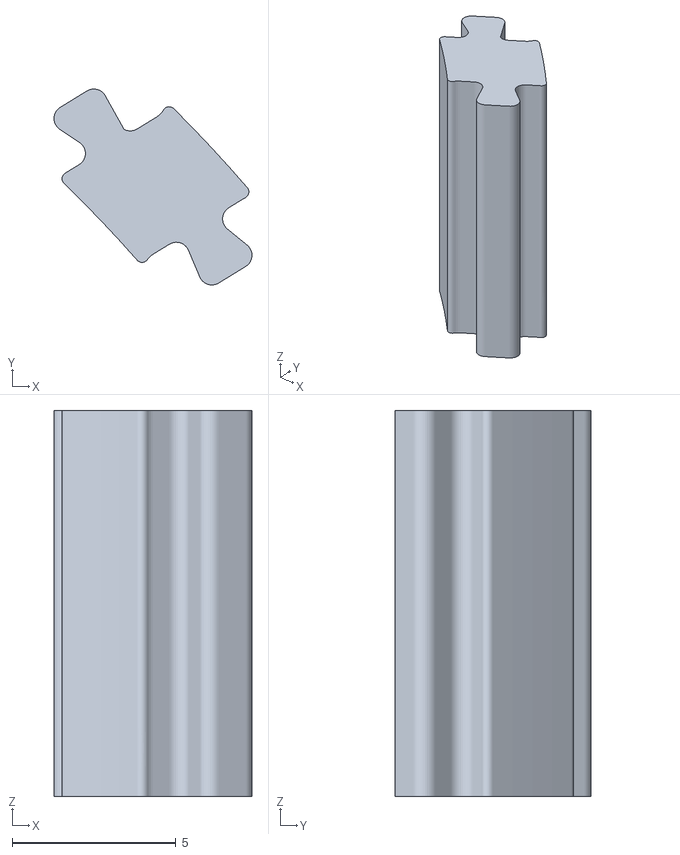
[picture p143: CAD file, 2024-03-13]
STLs/1_FlowChamber/1.5_FanWirePin_Spare.stl
6.05 x 5.99 x 11.8
