nevermore3d/StealthMax/STLs/2_MainChamber/StealthMax/M_2.2d_CarbonBasketLid_MMU_noHandles.3mf

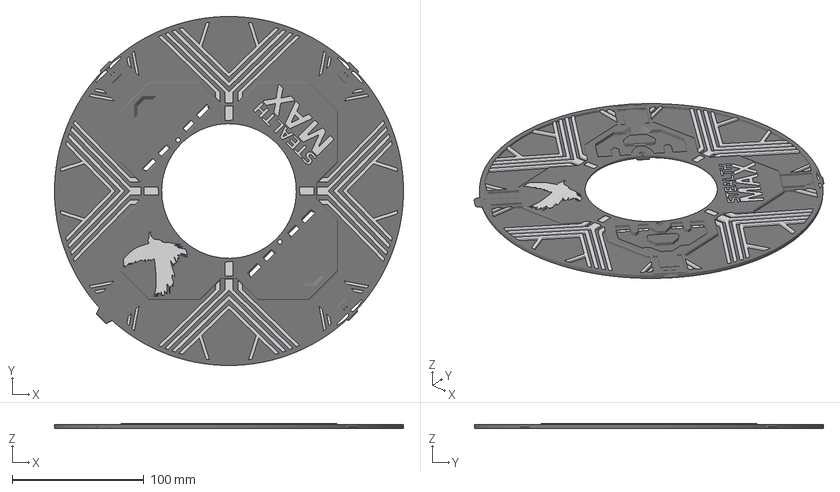
[picture p144: CAD file, 2024-03-18]
STLs/2_MainChamber/StealthMax/M_2.2d_CarbonBasketLid_MMU_noHandles.3mf
265.3 x 265.3 x 3.60 mm
