nevermore3d/StealthMax/STLs/4_AddOns/4.0_CPAPTubeIntake/4.0.3_IntakeRight.stl

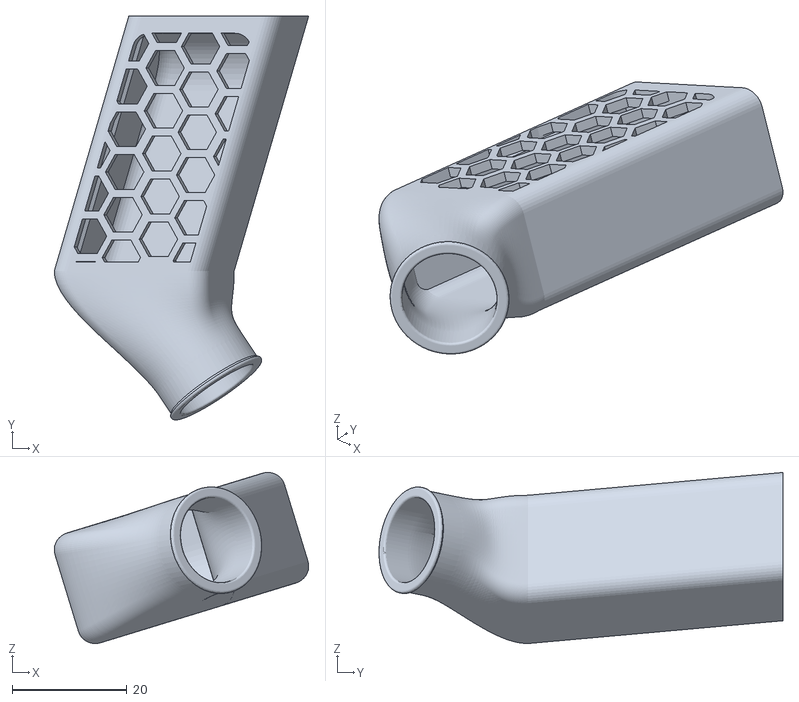
[picture p146: CAD file, 2024-08-18]
STLs/4_AddOns/4.0_CPAPTubeIntake/4.0.3_IntakeRight.stl
44.3 x 70.4 x 29.8
