nevermore3d/StealthMax/STLs/4_AddOns/4.1_PCOFiltration/4.1.0_PCOChamberUVC.stl

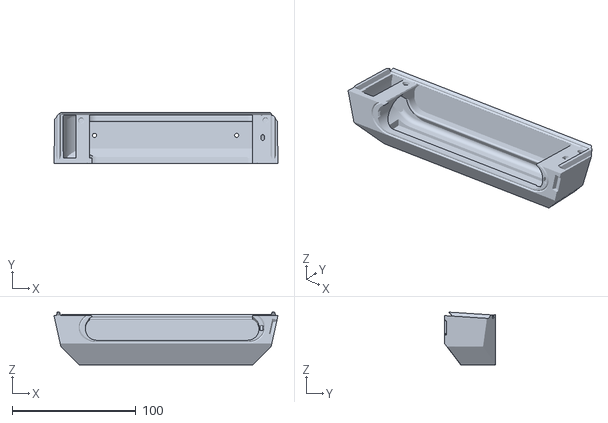
[picture p147: CAD file, 2024-03-13]
STLs/4_AddOns/4.1_PCOFiltration/4.1.0_PCOChamberUVC.stl
181.3 x 41.2 x 42.7
