nevermore3d/StealthMax/UserMods/[Parametric] Exhaust Pipe (by FatalBulletHit)/STLs/ExhaustPipe_DOPM_5mm.stl

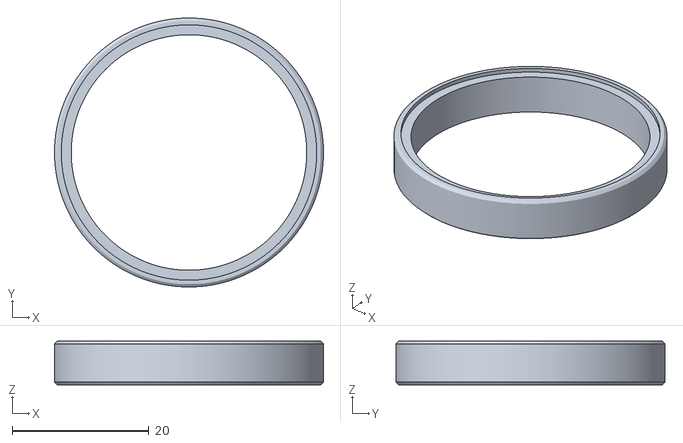
[picture p148: CAD file, 2024-03-18]
UserMods/[Parametric] Exhaust Pipe (by FatalBulletHit)/STLs/ExhaustPipe_DOPM_5mm.stl
39.3 x 39.3 x 6.40
