nevermore3d/StealthMax/UserMods/Ghetto Panel (by TessaKavanagh)/S_GhettoPanel.stl

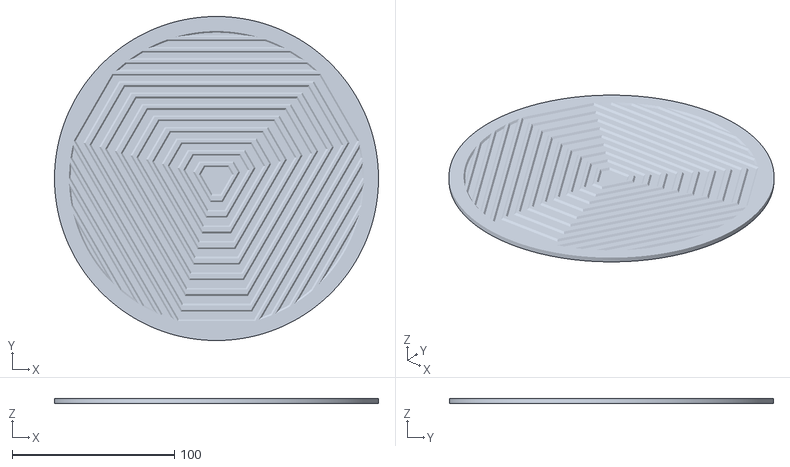
[picture p150: CAD file, 2024-03-13]
UserMods/Ghetto Panel (by TessaKavanagh)/S_GhettoPanel.stl
200.0 x 200.0 x 3.00
