nevermore3d/StealthMax/UserMods/Toggleable Channel DOPM FlowChamber (by VIN-y)/CADs/10_NM_StealthMax_Mod-Swich_Leave.step

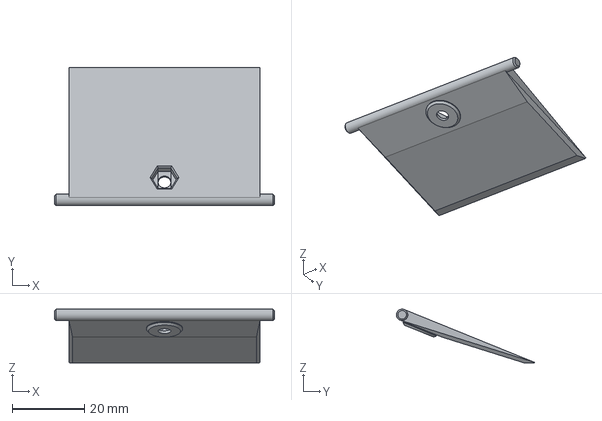
[picture p151: CAD file, 2024-10-18]
UserMods/Toggleable Channel DOPM FlowChamber (by VIN-y)/CADs/10_NM_StealthMax_Mod-Swich_Leave.step
60.7 x 38.1 x 14.8 mm
