nevermore3d/StealthMax/UserMods/Voron Exhaust Fitting - ERCF Filament Motion Sensor (by ManuC)/M_VoronExhaustFitting_BPM_ERCF_SFS.stl

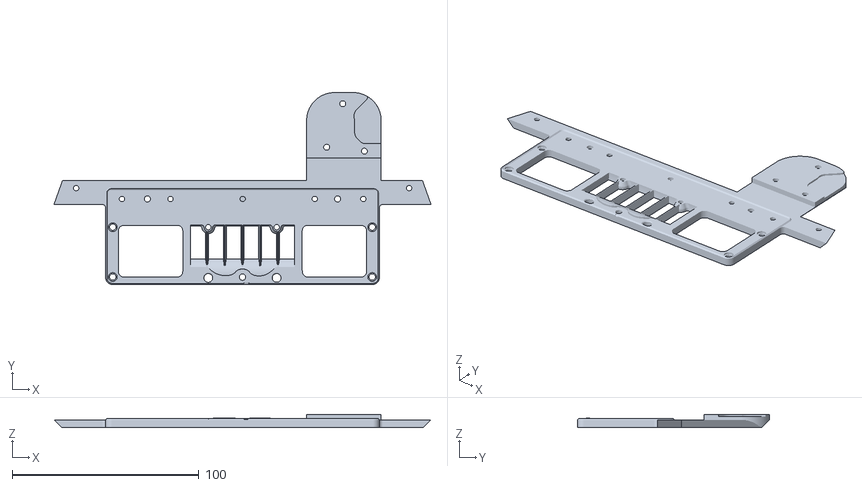
[picture p152: CAD file, 2024-03-13]
UserMods/Voron Exhaust Fitting - ERCF Filament Motion Sensor (by ManuC)/M_VoronExhaustFitting_BPM_ERCF_SFS.stl
202.0 x 102.8 x 6.75
