nevermore3d/StealthMax/STLs/1_FlowChamber/1.3b_BowdenCap_Open.stl

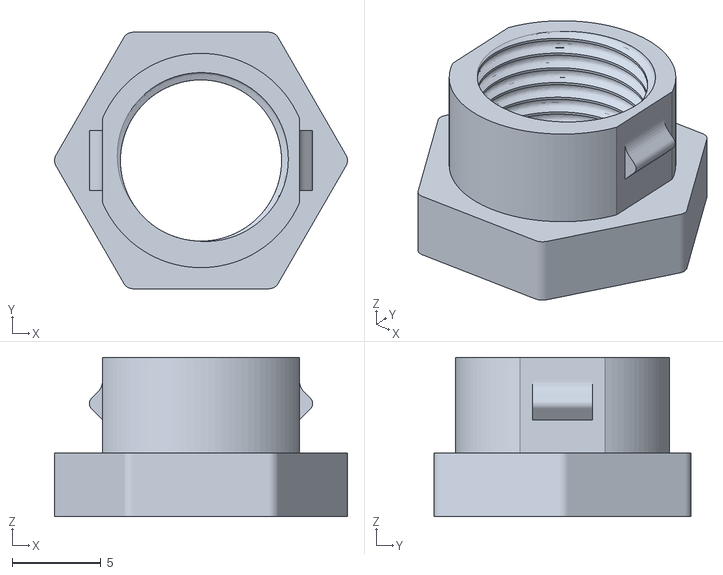
[picture p153: CAD file, 2024-03-13]
STLs/1_FlowChamber/1.3b_BowdenCap_Open.stl
16.5 x 14.5 x 9.00
