nevermore3d/StealthMax/STLs/2_MainChamber/StealthMax/M_2.2a_CarbonBasketLid.stl

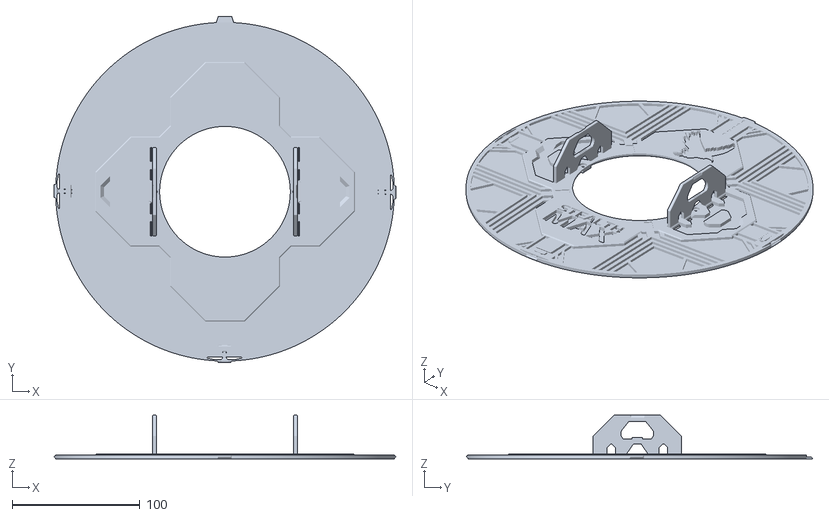
[picture p154: CAD file, 2024-03-18]
STLs/2_MainChamber/StealthMax/M_2.2a_CarbonBasketLid.stl
267.9 x 271.4 x 34.1
