nevermore3d/StealthMax/STLs/2_MainChamber/StealthMax_S/S_2.3_HEPACover.stl

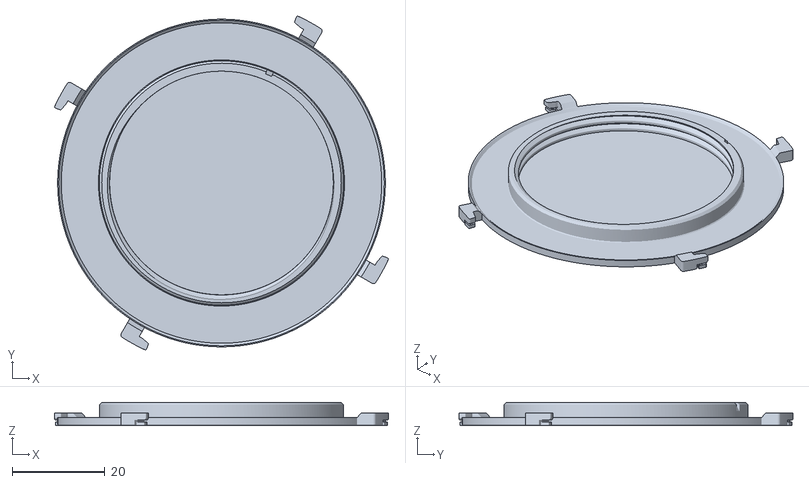
[picture p155: CAD file, 2024-03-18]
STLs/2_MainChamber/StealthMax_S/S_2.3_HEPACover.stl
72.0 x 72.0 x 5.00
