nevermore3d/StealthMax/STLs/4_AddOns/4.1_PCOFiltration/4.1.3_PCOFilterCover.stl

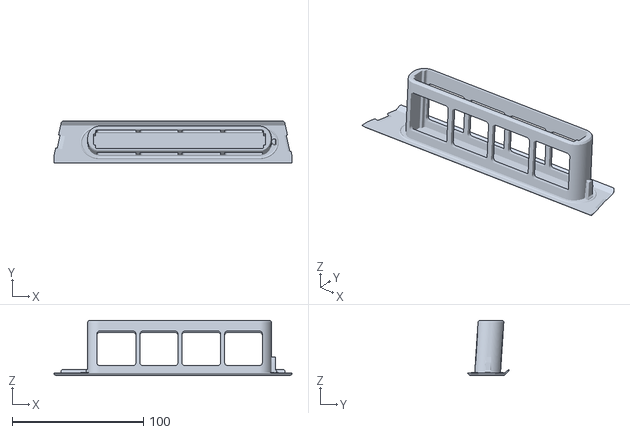
[picture p156: CAD file, 2024-03-13]
STLs/4_AddOns/4.1_PCOFiltration/4.1.3_PCOFilterCover.stl
181.3 x 31.6 x 42.0
