nevermore3d/StealthMax/UserMods/[Parametric] Voron Exhaust Fitting (by Rock270)/STLs/M_VoronExhaustFitting_BPM_8mm.stl

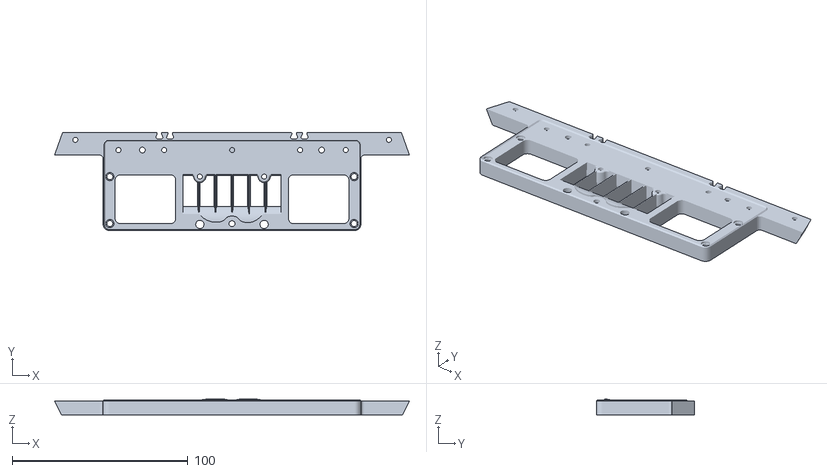
[picture p157: CAD file, 2023-12-09]
UserMods/[Parametric] Voron Exhaust Fitting (by Rock270)/STLs/M_VoronExhaustFitting_BPM_8mm.stl
202.0 x 55.8 x 9.00
