nevermore3d/StealthMax/UserMods/Toggleable Channel DOPM FlowChamber (by VIN-y)/CADs/10_NM_StealthMax_Mod-Output_Funnel.step

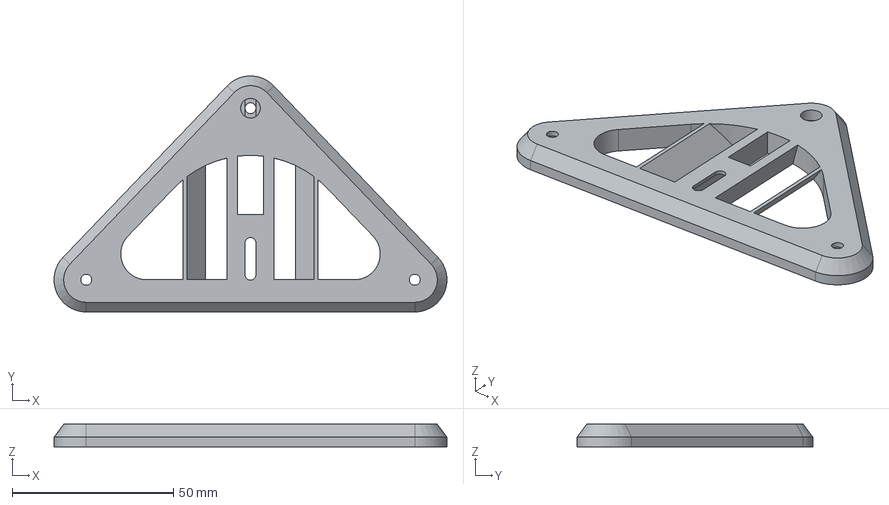
[picture p158: CAD file, 2024-10-18]
UserMods/Toggleable Channel DOPM FlowChamber (by VIN-y)/CADs/10_NM_StealthMax_Mod-Output_Funnel.step
121.9 x 73.2 x 7.00 mm
