nevermore3d/StealthMax/UserMods/Voron Exhaust Fitting - ERCF Filament Motion Sensor (by ManuC)/Voron Exhaust Fitting ERCF Filament Motion Sensor (by ManuC).step

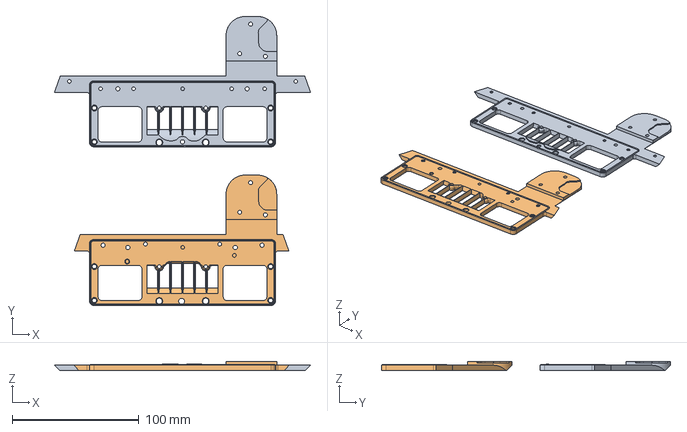
[picture p159: CAD file, 2024-03-13]
UserMods/Voron Exhaust Fitting - ERCF Filament Motion Sensor (by ManuC)/Voron Exhaust Fitting ERCF Filament Motion Sensor (by ManuC).step
202.0 x 227.8 x 6.76 mm
SM_300
SM_S_250
