nevermore3d/StealthMax/STLs/1_FlowChamber/1.4c_CableEntryCap_Closed.stl

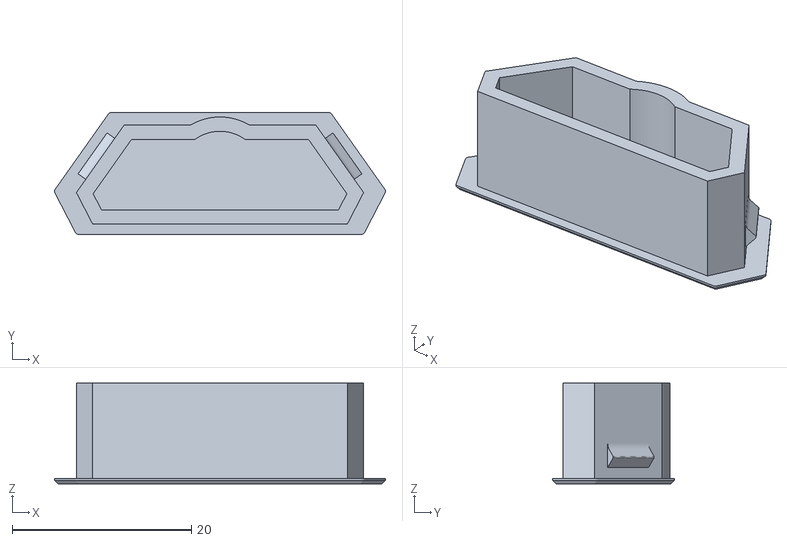
[picture p160: CAD file, 2024-03-13]
STLs/1_FlowChamber/1.4c_CableEntryCap_Closed.stl
36.9 x 13.6 x 11.3
