nevermore3d/StealthMax/STLs/2_MainChamber/StealthMax/M_2.2b_CarbonBasketLid_noHandles.stl

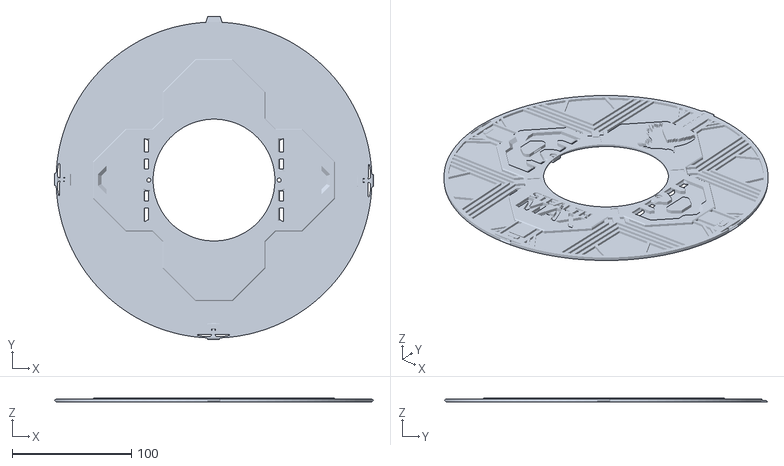
[picture p161: CAD file, 2024-03-18]
STLs/2_MainChamber/StealthMax/M_2.2b_CarbonBasketLid_noHandles.stl
267.9 x 271.4 x 3.60
