nevermore3d/StealthMax/STLs/2_MainChamber/StealthMax_S/S_2.6a_PicoAccessLatch.stl

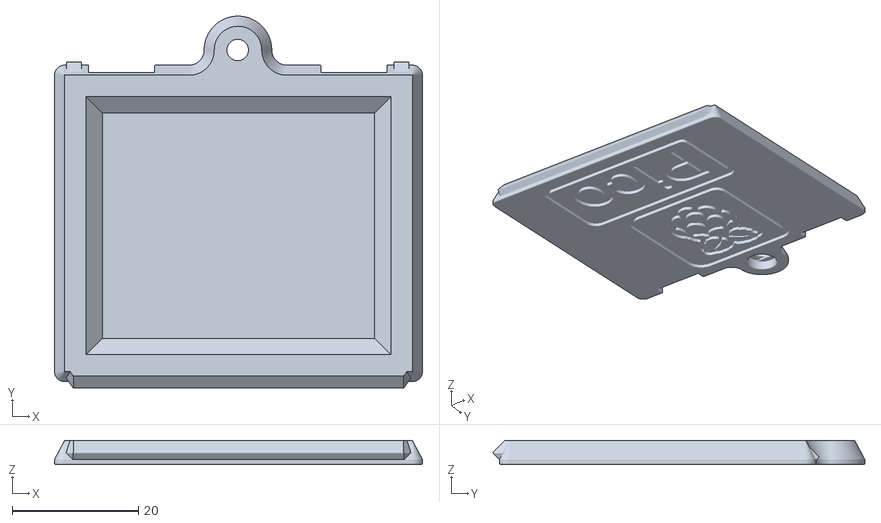
[picture p162: CAD file, 2024-03-18]
STLs/2_MainChamber/StealthMax_S/S_2.6a_PicoAccessLatch.stl
58.2 x 58.8 x 3.80
