nevermore3d/StealthMax/UserMods/Toggleable Channel DOPM FlowChamber (by VIN-y)/CADs/10_NM_StealthMax_Mod-FlowChamber_Mod.step

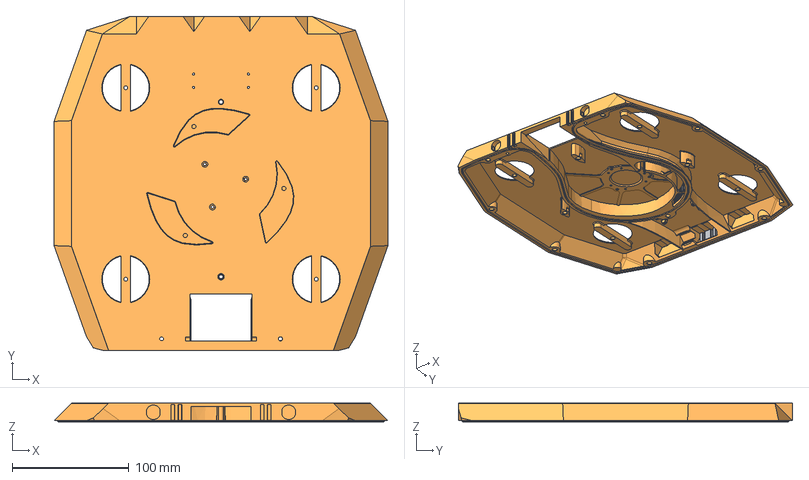
[picture p164: CAD file, 2024-10-18]
UserMods/Toggleable Channel DOPM FlowChamber (by VIN-y)/CADs/10_NM_StealthMax_Mod-FlowChamber_Mod.step
286.4 x 286.4 x 15.9 mm
DOPM_Modded-Body
Spare_Slot_Support_Design-Body
Spare_Slot_1_Support-Body
Spare_Slot_2_Support-Body
Spare_Slot_3_Support-Body
Cable_Channel_Support-Body
