nevermore3d/StealthMax/STLs/1_FlowChamber/1.2_AirExhaustSlider.stl

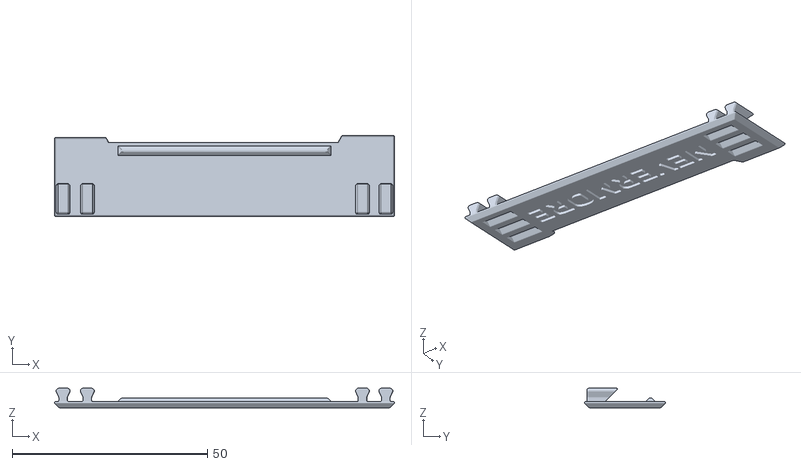
[picture p166: CAD file, 2024-03-13]
STLs/1_FlowChamber/1.2_AirExhaustSlider.stl
87.2 x 20.7 x 5.00
