nevermore3d/StealthMax/STLs/2_MainChamber/StealthMax/M_2.2c_CarbonBasketLid_MMU.3mf

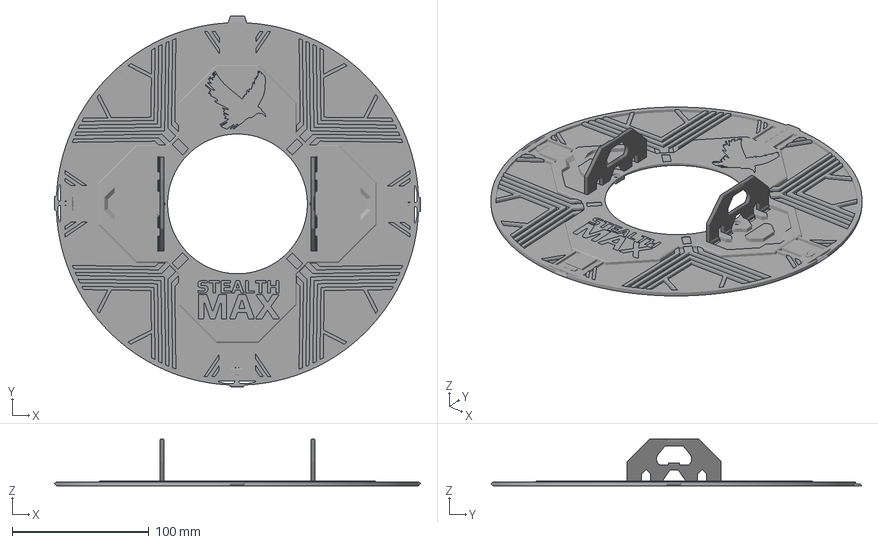
[picture p167: CAD file, 2024-03-18]
STLs/2_MainChamber/StealthMax/M_2.2c_CarbonBasketLid_MMU.3mf
267.9 x 271.4 x 34.1 mm
