nevermore3d/StealthMax/STLs/2_MainChamber/StealthMax_S/S_2.7_IntakeSensorStackAccessLatch.stl

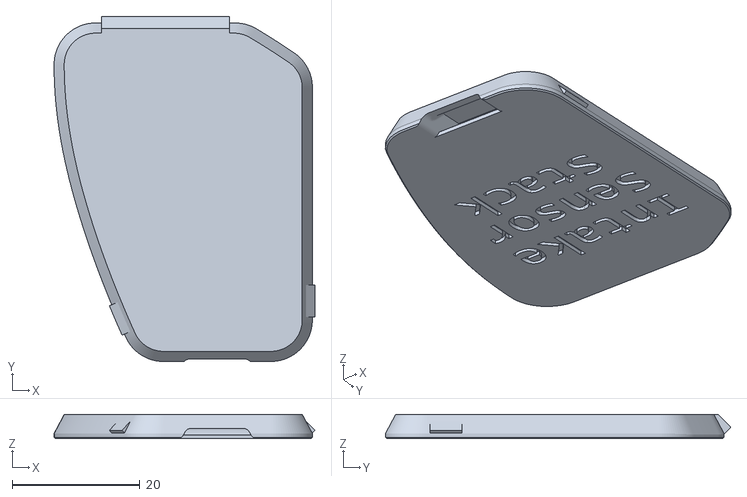
[picture p168: CAD file, 2024-03-18]
STLs/2_MainChamber/StealthMax_S/S_2.7_IntakeSensorStackAccessLatch.stl
40.8 x 54.0 x 3.80
