nevermore3d/StealthMax/STLs/1_FlowChamber/1.4b_CableEntryCap_MicroFit3.stl

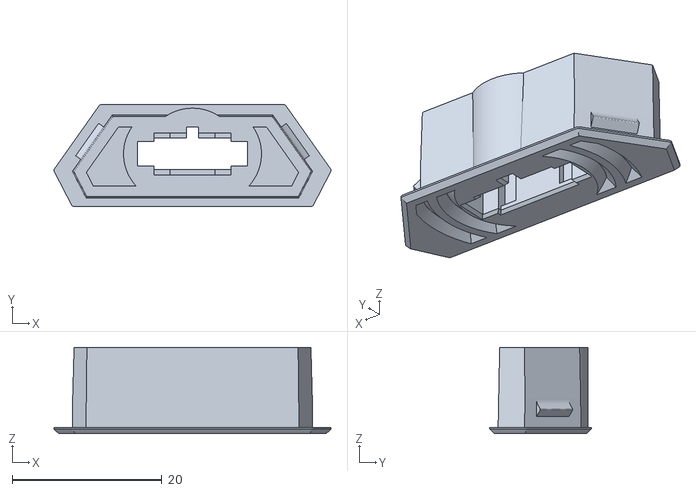
[picture p170: CAD file, 2024-03-13]
STLs/1_FlowChamber/1.4b_CableEntryCap_MicroFit3.stl
36.9 x 13.6 x 11.5
