nevermore3d/StealthMax/STLs/2_MainChamber/StealthMax/M_2.7_IntakeSensorStackAccessLatch.stl

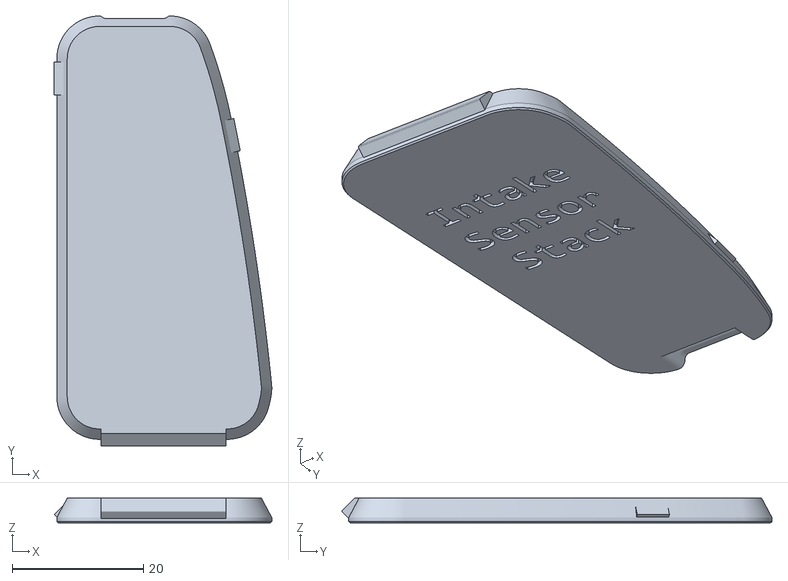
[picture p171: CAD file, 2024-03-13]
STLs/2_MainChamber/StealthMax/M_2.7_IntakeSensorStackAccessLatch.stl
33.1 x 65.5 x 3.80
