nevermore3d/StealthMax/STLs/2_MainChamber/StealthMax_S/S_2.2a_CarbonBasketLid.stl

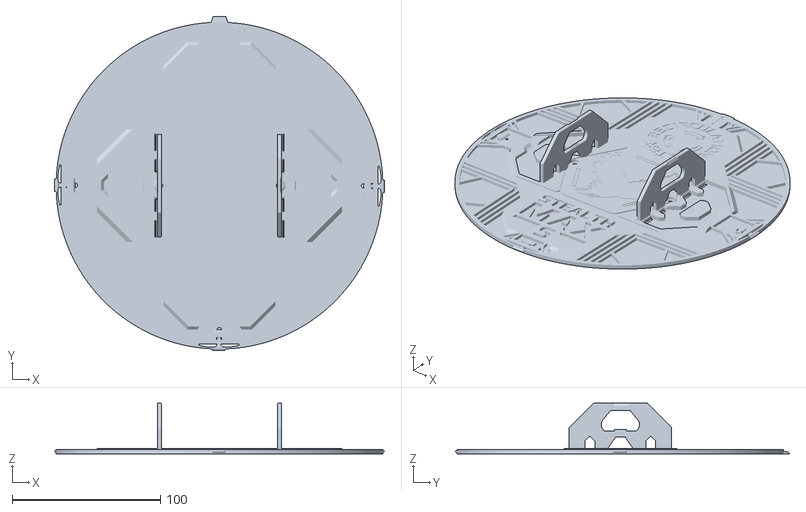
[picture p172: CAD file, 2024-03-18]
STLs/2_MainChamber/StealthMax_S/S_2.2a_CarbonBasketLid.stl
222.4 x 225.3 x 34.1
