nevermore3d/StealthMax/UserMods/Toggleable Channel DOPM FlowChamber (by VIN-y)/CADs/10_NM_StealthMax_Mod-Top_Panel_300_Laser_Cut.step

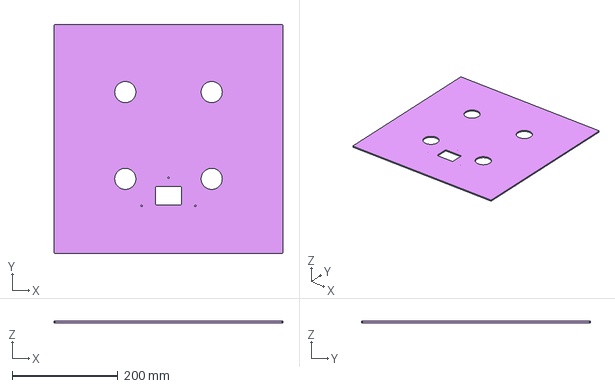
[picture p173: CAD file, 2024-10-18]
UserMods/Toggleable Channel DOPM FlowChamber (by VIN-y)/CADs/10_NM_StealthMax_Mod-Top_Panel_300_Laser_Cut.step
433.0 x 433.0 x 3.00 mm
