nevermore3d/StealthMax/STLs/2_MainChamber/StealthMax/M_2.4_HEPAPryerTool_Spare.stl

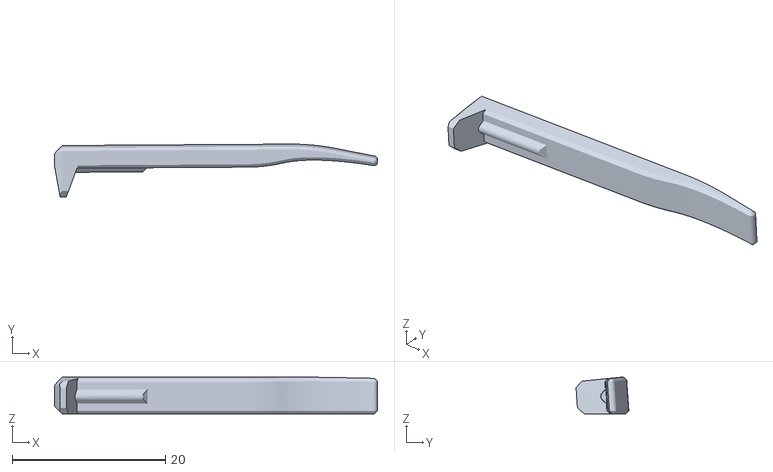
[picture p174: CAD file, 2024-03-13]
STLs/2_MainChamber/StealthMax/M_2.4_HEPAPryerTool_Spare.stl
42.1 x 6.89 x 4.81
