nevermore3d/StealthMax/STLs/2_MainChamber/StealthMax_S/S_2.6b_PicoAccessLatch_MMU.3mf

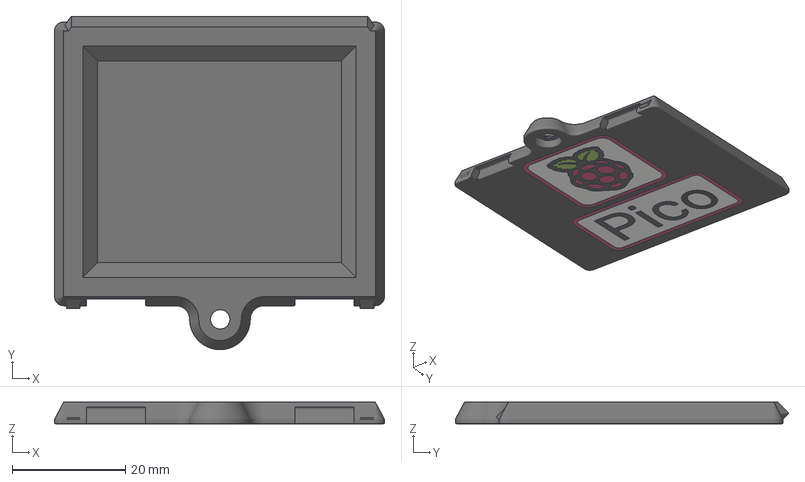
[picture p175: CAD file, 2024-03-18]
STLs/2_MainChamber/StealthMax_S/S_2.6b_PicoAccessLatch_MMU.3mf
58.2 x 58.8 x 3.80 mm
