nevermore3d/StealthMax/STLs/2_MainChamber/StealthMax/M_2.3_HEPACover.stl

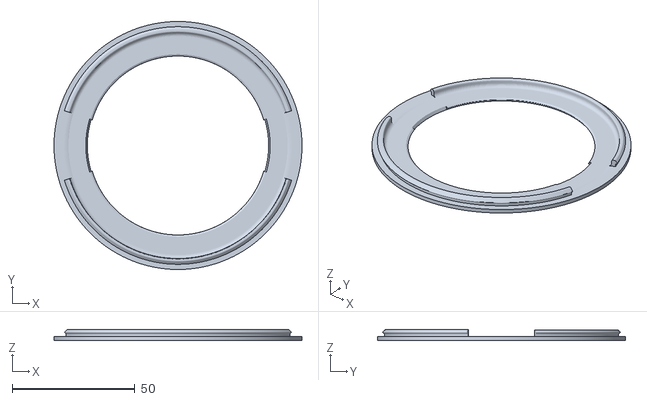
[picture p176: CAD file, 2024-03-13]
STLs/2_MainChamber/StealthMax/M_2.3_HEPACover.stl
101.0 x 101.0 x 4.68
