nevermore3d/StealthMax/STLs/2_MainChamber/StealthMax_S/S_2.2d_CarbonBasketLid_MMU_noHandles.3mf

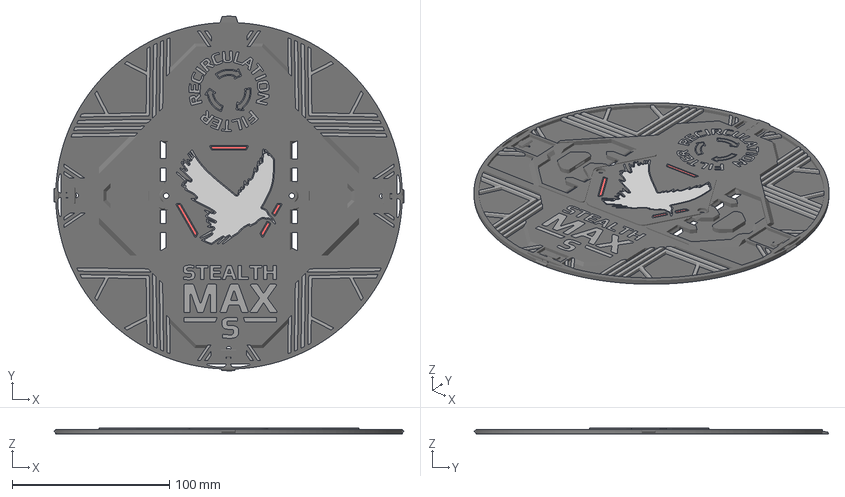
[picture p177: CAD file, 2024-03-18]
STLs/2_MainChamber/StealthMax_S/S_2.2d_CarbonBasketLid_MMU_noHandles.3mf
222.4 x 225.3 x 3.67 mm
