nevermore3d/StealthMax/STLs/2_MainChamber/StealthMax/M_2.8_BowdenTubeAccessLatch.stl

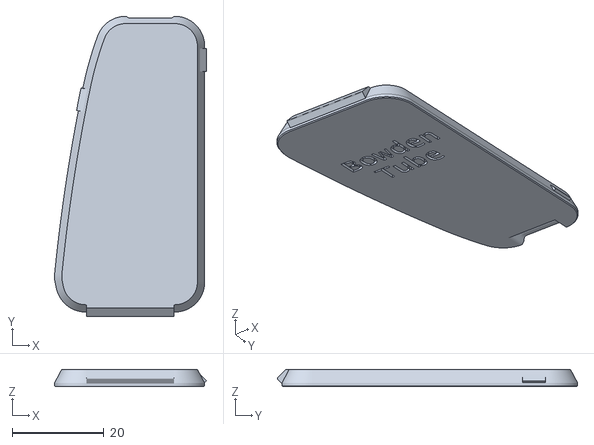
[picture p178: CAD file, 2024-03-13]
STLs/2_MainChamber/StealthMax/M_2.8_BowdenTubeAccessLatch.stl
33.1 x 65.5 x 3.80
