nevermore3d/StealthMax/STLs/2_MainChamber/StealthMax_S/S_2.2b_CarbonBasketLid_noHandles.stl

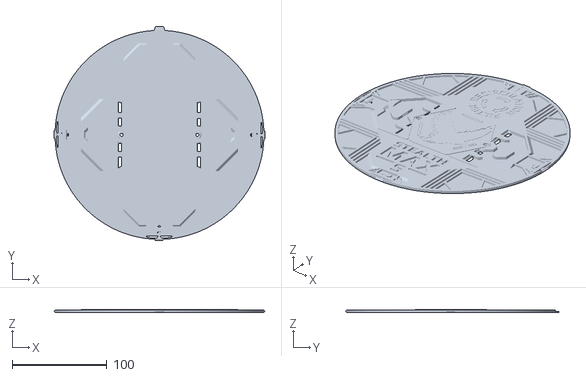
[picture p179: CAD file, 2024-03-18]
STLs/2_MainChamber/StealthMax_S/S_2.2b_CarbonBasketLid_noHandles.stl
222.4 x 225.3 x 3.67
