nevermore3d/StealthMax/STLs/2_MainChamber/StealthMax/M_2.6b_PicoAccessLatch_MMU.3mf

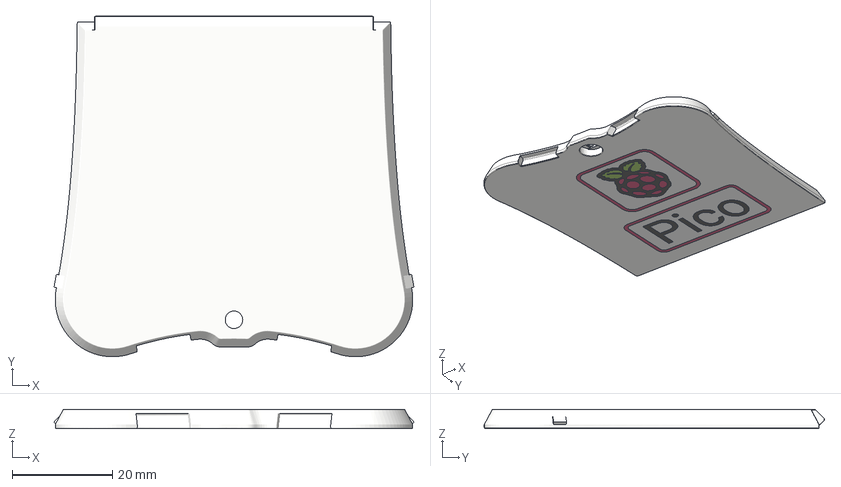
[picture p180: CAD file, 2024-03-07]
STLs/2_MainChamber/StealthMax/M_2.6b_PicoAccessLatch_MMU.3mf
71.7 x 67.9 x 3.80 mm
