nevermore3d/StealthMax/STLs/2_MainChamber/StealthMax_S/S_2.2c_CarbonBasketLid_MMU.3mf

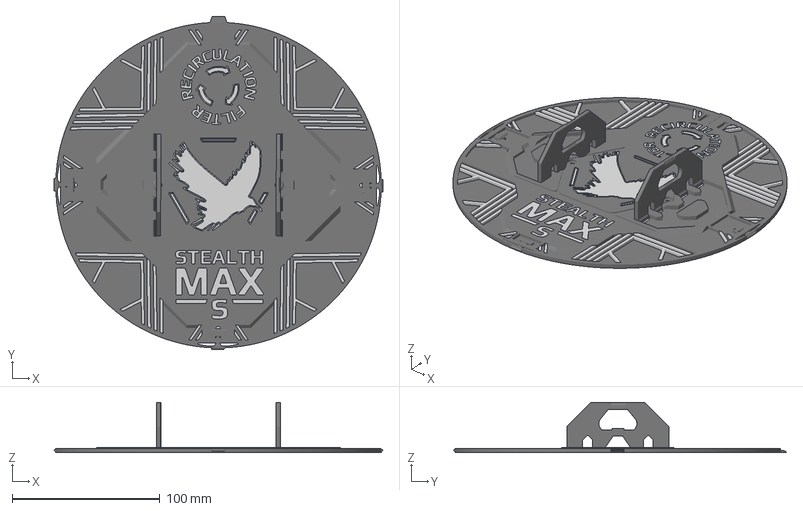
[picture p181: CAD file, 2024-03-18]
STLs/2_MainChamber/StealthMax_S/S_2.2c_CarbonBasketLid_MMU.3mf
222.4 x 225.3 x 34.1 mm
