nevermore3d/StealthMax/STLs/2_MainChamber/StealthMax/M_2.6a_PicoAccessLatch.stl

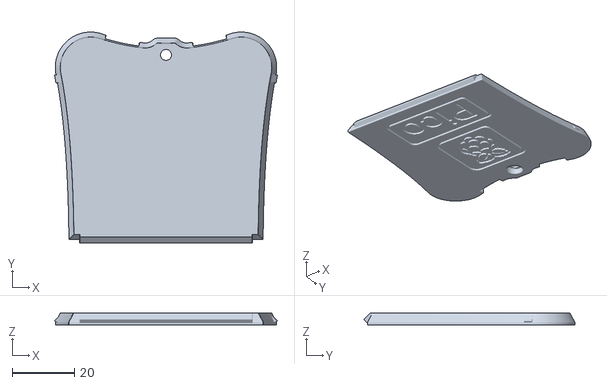
[picture p182: CAD file, 2024-03-07]
STLs/2_MainChamber/StealthMax/M_2.6a_PicoAccessLatch.stl
71.7 x 67.9 x 3.80
