nevermore3d/StealthMax/assets/docs/BPM/bpm_electronics_buck_converter_soldered2.png.JPEG

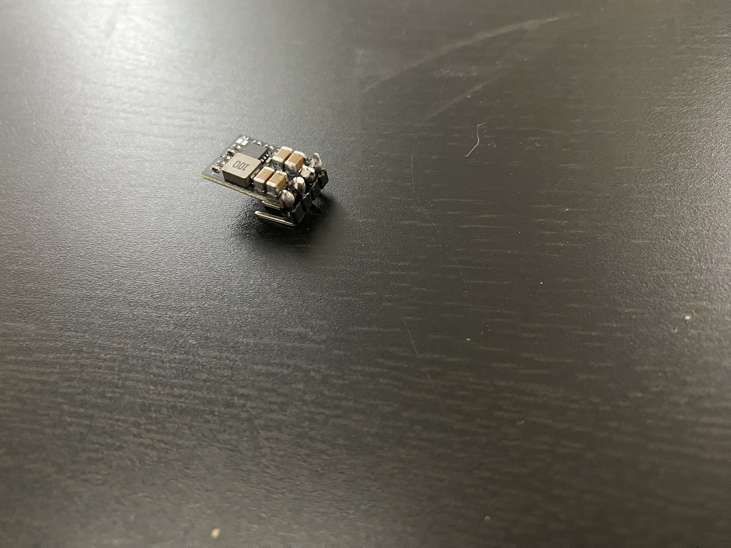
assets/docs/BPM/bpm_electronics_buck_converter_soldered2.png.JPEG
